jimcan92/research-weather-station/docs/schematic-mosfet-switch.html

# MOSFET Switch — 12V Wind Sensor Power

IRF4905 (P-channel) + 2N7000 (N-channel) · high-side switch · control from GPIO15

## Schematic

## How it works

GPIO15 | Q2 (2N7000) | Q1 (IRF4905) gate | 12V_SW output
LOW (0V) | OFF | pulled to +12V via R1 | 0V — sensors OFF
HIGH (3.3V) | ON | pulled to GND | 12V — sensors ON

Ngano ingon ani: Ang ESP32 3.3V ra ang iyang i-output, pero ang wind sensors nagkinahanglan og 12V. Ang 2N7000 (gagmay, 3.3V-driven) maoy mo-pull-down sa gate sa IRF4905 (dako, 12V) aron mo-ON kini. Ang R1 (10k) kay pull-up — nag-keep sa IRF4905 nga OFF by default para dili aksidente nga mo-on ang 12V samtang natulog ang ESP32.

## Parts list

Ref | Part | Type | Role
Q1 | IRF4905 | P-channel MOSFET (TO-220) | 12V high-side switch
Q2 | 2N7000 | N-channel MOSFET (TO-92) | Level shifter (3.3V → drive Q1 gate)
R1 | 10kΩ | Resistor | Gate pull-up (default OFF)
R2 | 1kΩ | Resistor | Q2 gate resistor (limits GPIO current)
