jimcan92/research-weather-station/hardware/node-pcb/weather-node-complete-preview-1.png

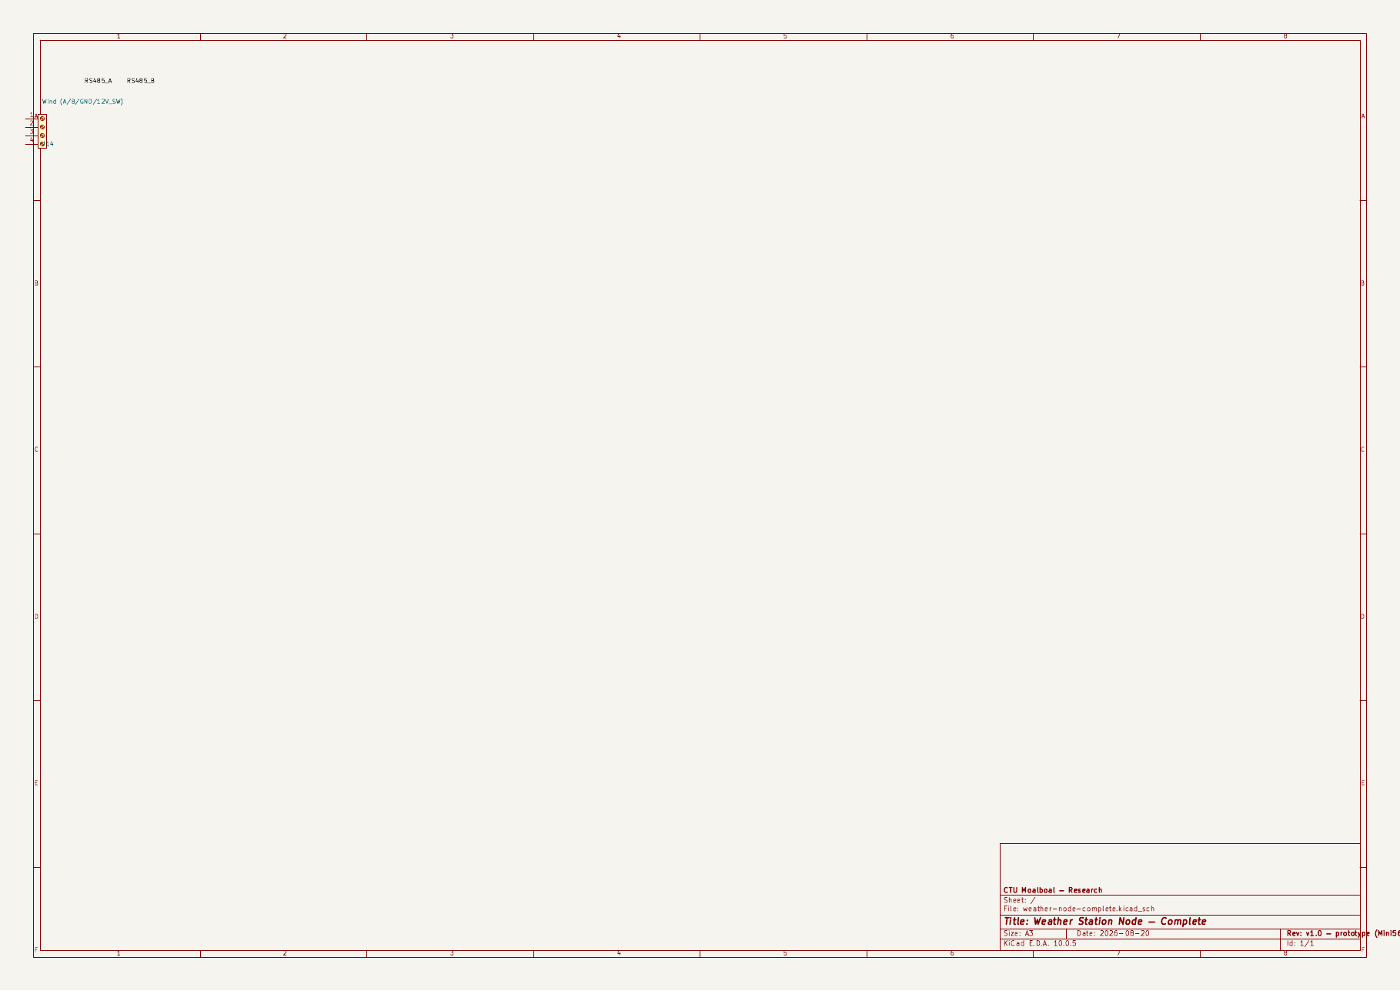
hardware/node-pcb/weather-node-complete-preview-1.png
