jimcan92/research-weather-station/output/schematic-review/lora-e22-current.png

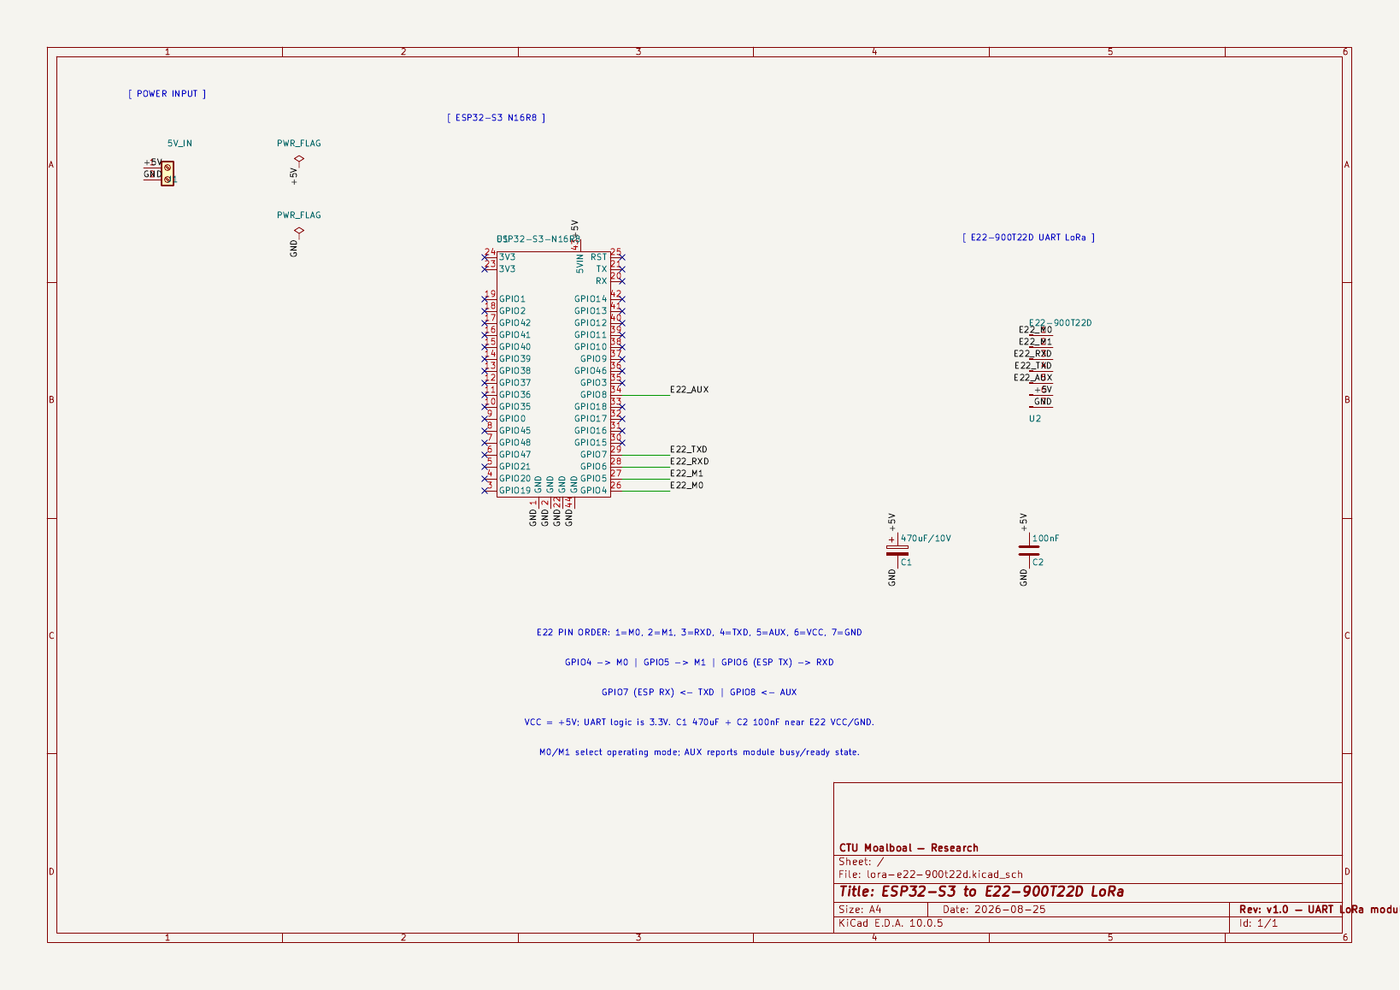
output/schematic-review/lora-e22-current.png
