jimcan92/research-weather-station/hardware/lora-e22/lora-e22-900t22d.kicad_sch

## KiCad design hardware/lora-e22/lora-e22-900t22d.kicad_sch (2026-09-29)

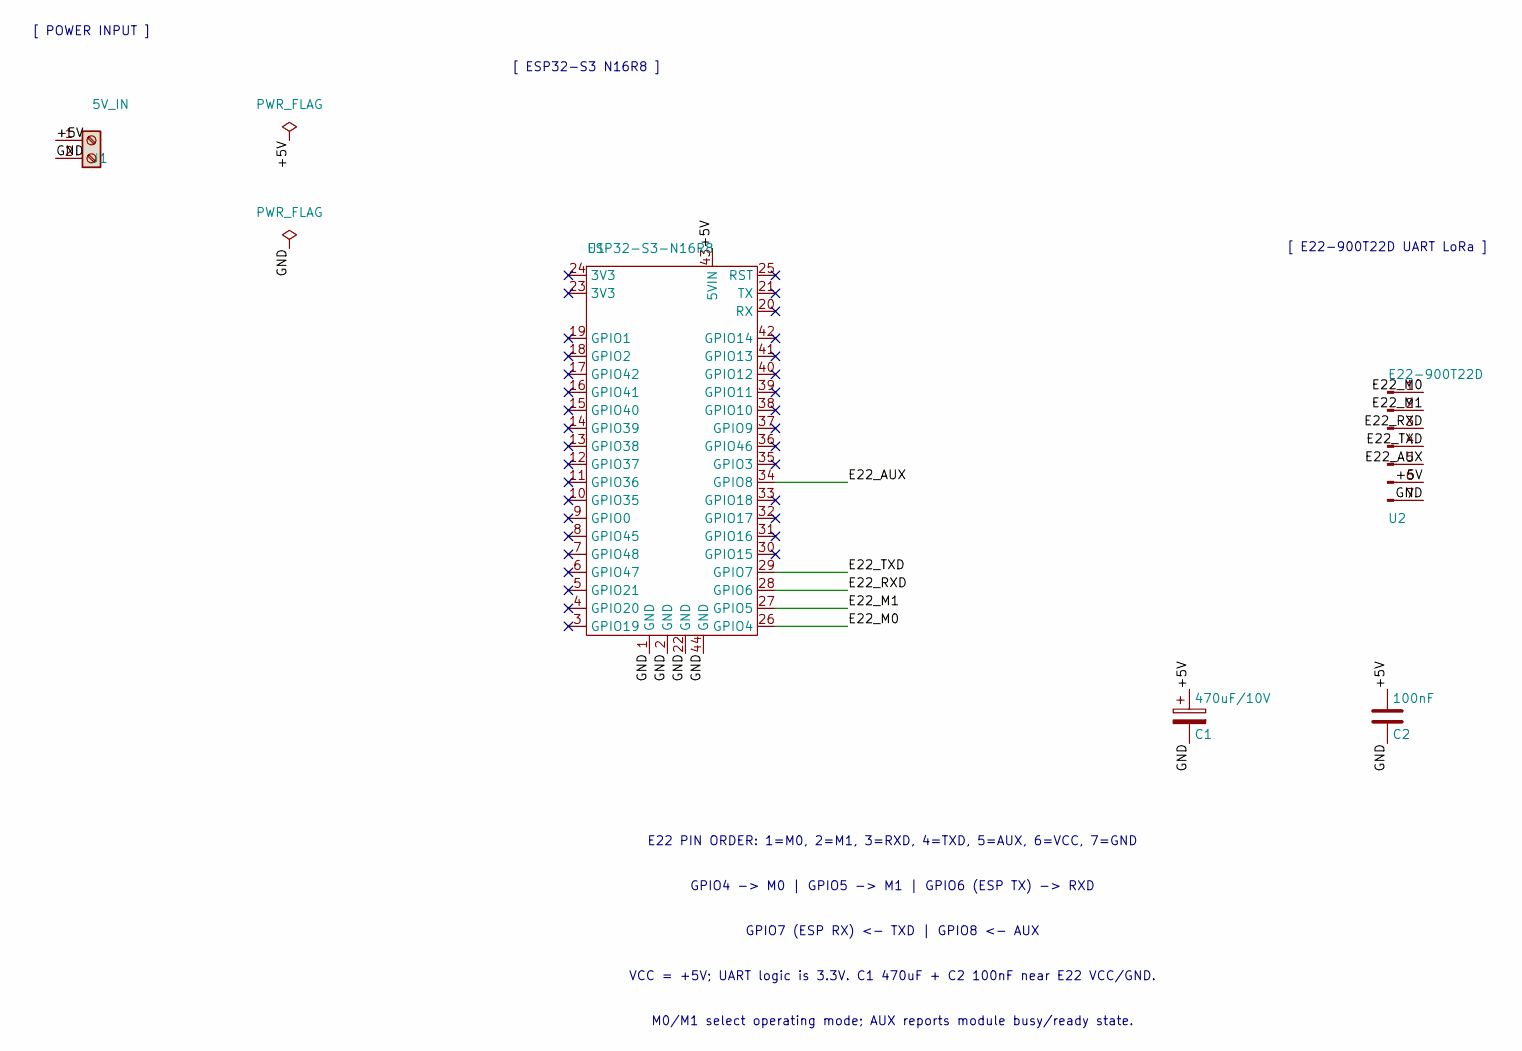
[picture p7: schematic lora-e22-900t22d.kicad_sch]

Parts:
C1: 470uF/10V
C2: 100nF
J1: 5V_IN
U1: ESP32-S3-N16R8
U2: E22-900T22D

Connections:
+5V: C1.1, C2.1, J1.1, U1.43 (5VIN), U2.6
E22_AUX: U1.34 (GPIO8), U2.5
E22_M0: U1.26 (GPIO4), U2.1
E22_M1: U1.27 (GPIO5), U2.2
E22_RXD: U1.28 (GPIO6), U2.3
E22_TXD: U1.29 (GPIO7), U2.4
GND: C1.2, C2.2, J1.2, U1.1 (GND), U1.2 (GND), U1.22 (GND), U1.44 (GND), U2.7

Notes on the sheet:
[ POWER INPUT ]
[ ESP32-S3 N16R8 ]
[ E22-900T22D UART LoRa ]
E22 PIN ORDER: 1=M0, 2=M1, 3=RXD, 4=TXD, 5=AUX, 6=VCC, 7=GND
GPIO4 -> M0 | GPIO5 -> M1 | GPIO6 (ESP TX) -> RXD
GPIO7 (ESP RX) <- TXD | GPIO8 <- AUX
VCC = +5V; UART logic is 3.3V. C1 470uF + C2 100nF near E22 VCC/GND.
M0/M1 select operating mode; AUX reports module busy/ready state.
