jimcan92/research-weather-station/hardware/node-pcb/weather-node-complete.kicad_sch

## KiCad design hardware/node-pcb/weather-node-complete.kicad_sch (2026-09-29)

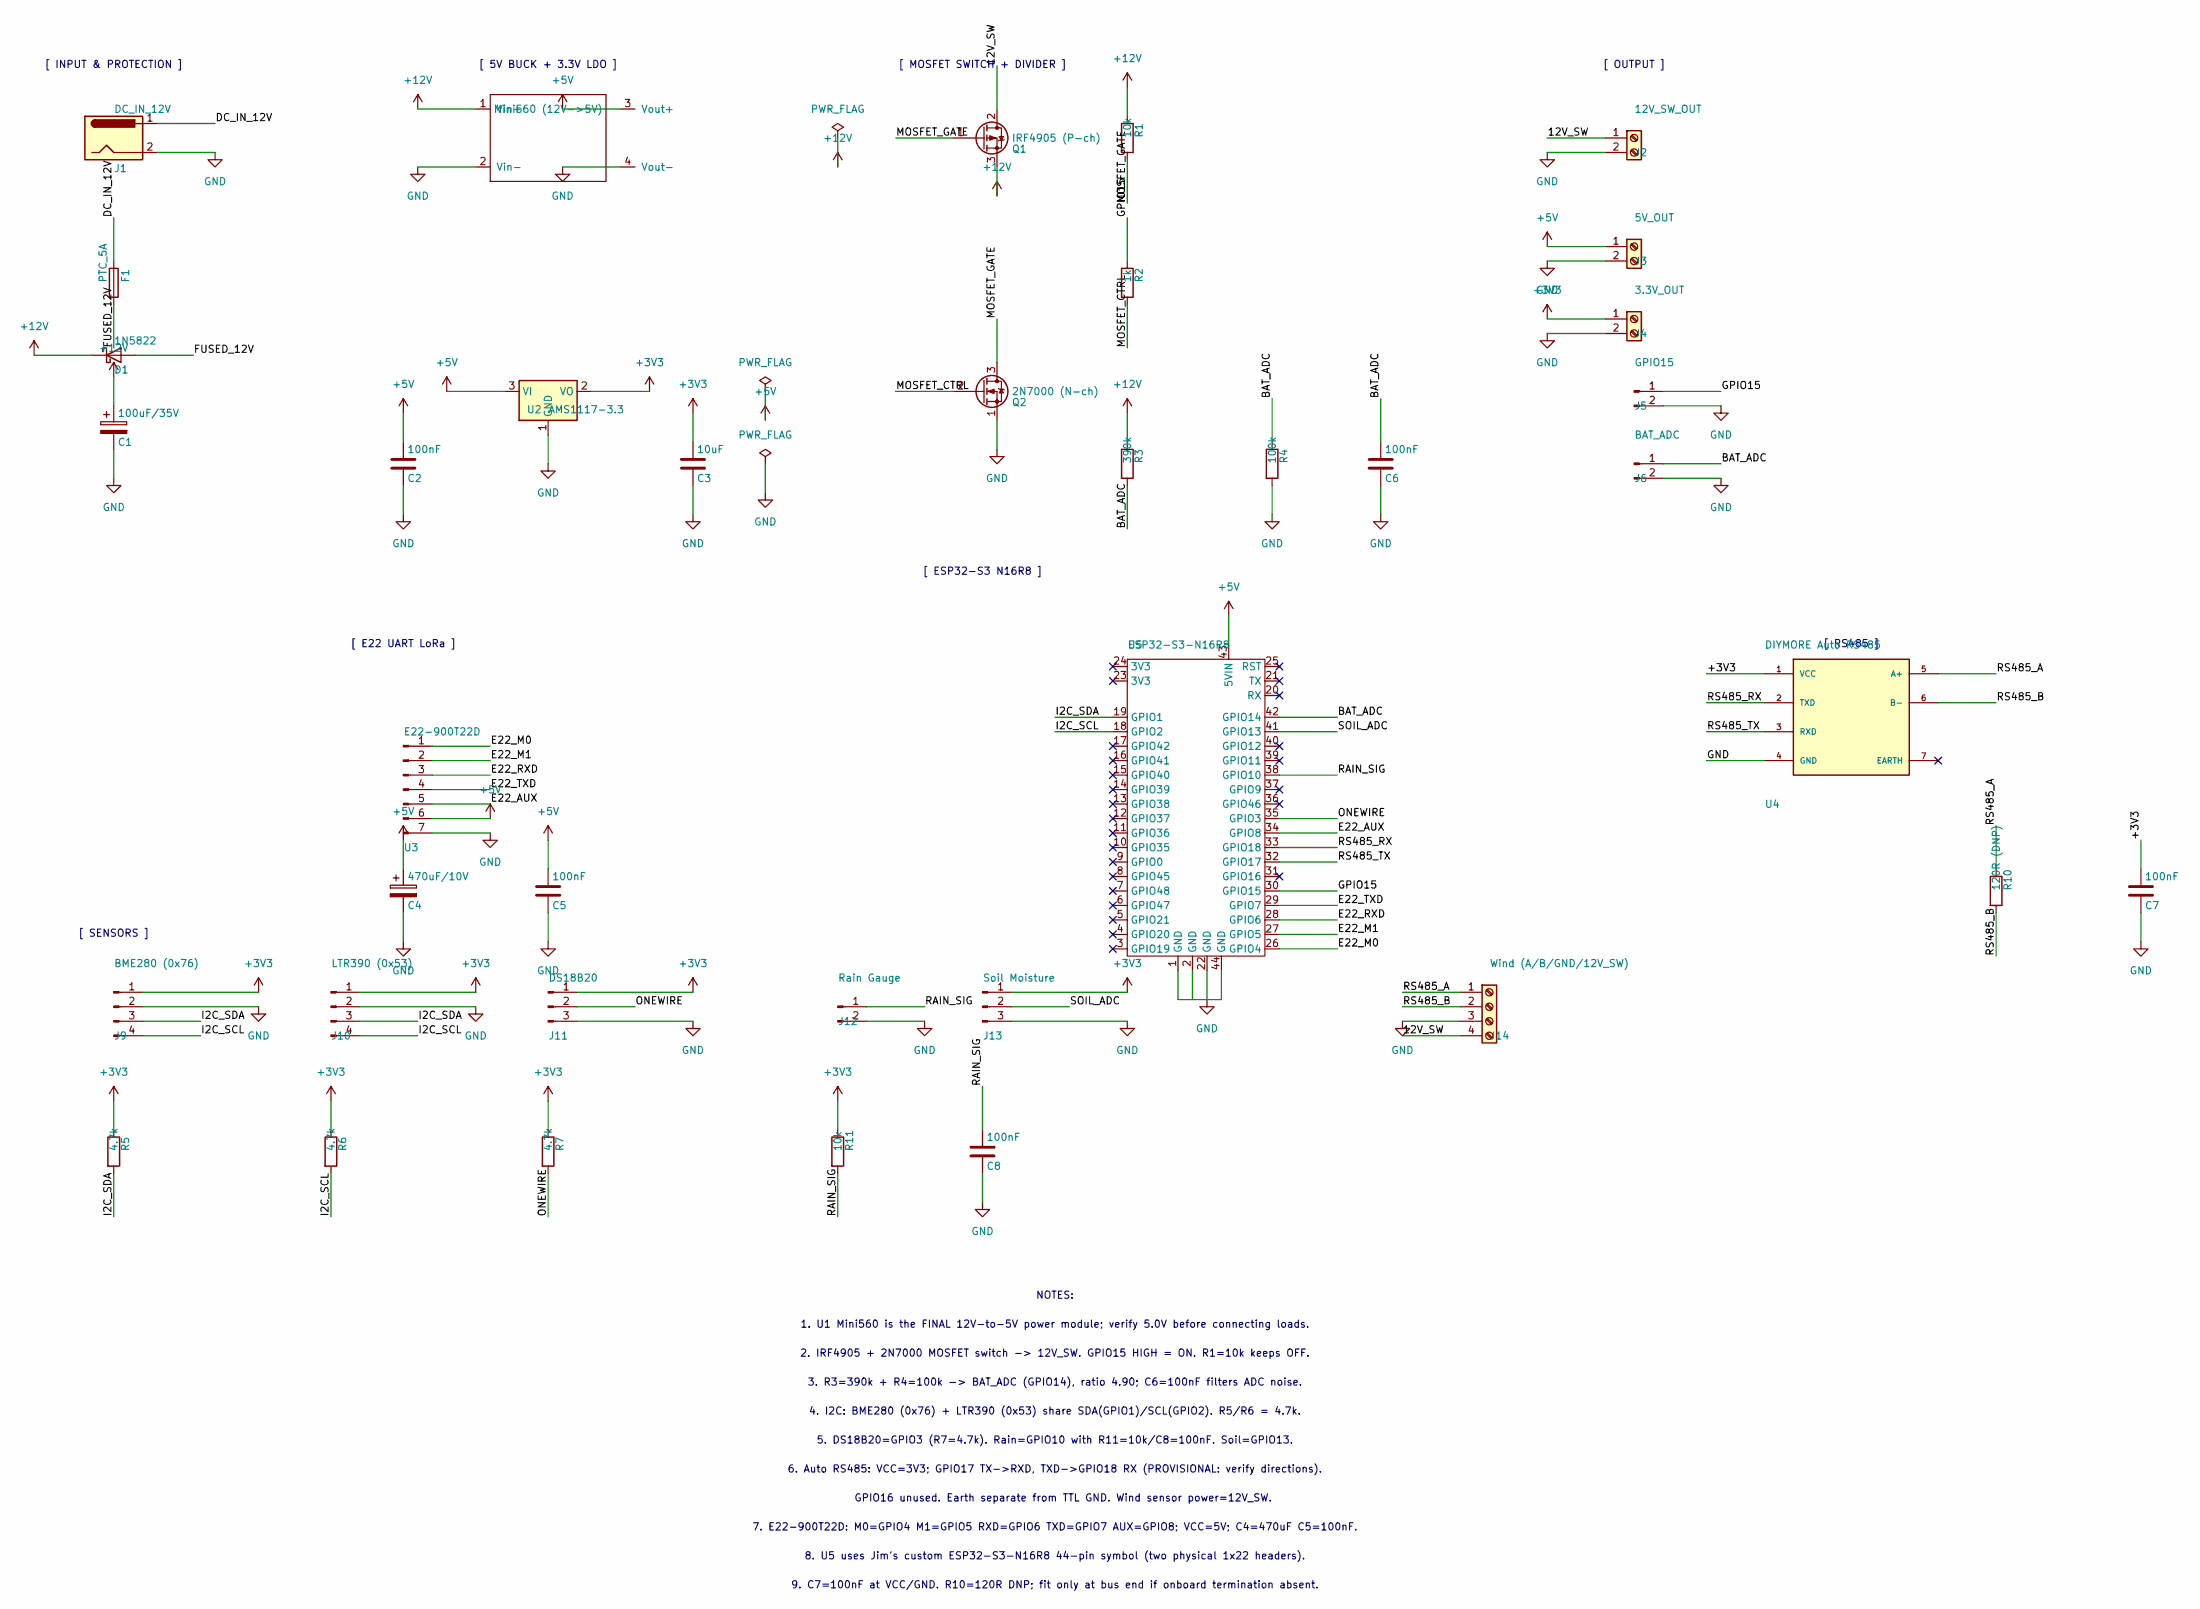
[picture p8: schematic weather-node-complete.kicad_sch]

Parts:
C1: 100uF/35V
C2, C5, C6, C7, C8: 100nF
C3: 10uF
C4: 470uF/10V
D1: 1N5822
F1: PTC_5A
J1: DC_IN_12V
J2: 12V_SW_OUT
J3: 5V_OUT
J4: 3.3V_OUT
J5: GPIO15
J6: BAT_ADC
J9: BME280 (0x76)
J10: LTR390 (0x53)
J11: DS18B20
J12: Rain Gauge
J13: Soil Moisture
J14: Wind (A/B/GND/12V_SW)
Q1: IRF4905 (P-ch)
Q2: 2N7000 (N-ch)
R1, R11: 10k
R2: 1k
R3: 390k
R4: 100k
R5, R6, R7: 4.7k
R10: 120R (DNP)
U1: Mini560 (12V->5V)
U2: AMS1117-3.3
U3: E22-900T22D
U4: DIYMORE Auto RS485
U5: ESP32-S3-N16R8

Connections:
12V_SW: J2.1, J14.4, Q1.2 (D)
+3V3: C3.1, C7.1, J4.1, J9.1, J10.1, J11.1, J13.1, R5.1, R6.1, R7.1, R11.1, U2.2 (VO), U4.1 (VCC)
+5V: C2.1, C4.1, C5.1, J3.1, U1.3 (Vout+), U2.3 (VI), U3.6, U5.43 (5VIN)
+12V: C1.1, D1.1 (K), Q1.3 (S), R1.1, R3.1, U1.1 (Vin+)
BAT_ADC: C6.1, J6.1, R3.2, R4.1, U5.42 (GPIO14)
DC_IN_12V: F1.1, J1.1
E22_AUX: U3.5, U5.34 (GPIO8)
E22_M0: U3.1, U5.26 (GPIO4)
E22_M1: U3.2, U5.27 (GPIO5)
E22_RXD: U3.3, U5.28 (GPIO6)
E22_TXD: U3.4, U5.29 (GPIO7)
FUSED_12V: D1.2 (A), F1.2
GND: C1.2, C2.2, C3.2, C4.2, C5.2, C6.2, C7.2, C8.2, J1.2, J2.2, J3.2, J4.2, J5.2, J6.2, J9.2, J10.2, J11.3, J12.2, J13.3, J14.3, Q2.1 (S), R4.2, U1.2 (Vin-), U1.4 (Vout-), U2.1 (GND), U3.7, U4.4 (GND), U5.1 (GND), U5.2 (GND), U5.22 (GND), U5.44 (GND)
GPIO15: J5.1, R2.1, U5.30 (GPIO15)
I2C_SCL: J9.4, J10.4, R6.2, U5.18 (GPIO2)
I2C_SDA: J9.3, J10.3, R5.2, U5.19 (GPIO1)
MOSFET_CTRL: Q2.2 (G), R2.2
MOSFET_GATE: Q1.1 (G), Q2.3 (D), R1.2
ONEWIRE: J11.2, R7.2, U5.35 (GPIO3)
RAIN_SIG: C8.1, J12.1, R11.2, U5.38 (GPIO10)
RS485_A: J14.1, R10.1, U4.5 (A+)
RS485_B: J14.2, R10.2, U4.6 (B-)
RS485_RX: U4.2 (TXD), U5.33 (GPIO18)
RS485_TX: U4.3 (RXD), U5.32 (GPIO17)
SOIL_ADC: J13.2, U5.41 (GPIO13)

Notes on the sheet:
[ INPUT & PROTECTION ]
[ 5V BUCK + 3.3V LDO ]
[ MOSFET SWITCH + DIVIDER ]
[ OUTPUT ]
[ ESP32-S3 N16R8 ]
[ E22 UART LoRa ]
[ RS485 ]
[ SENSORS ]
NOTES:
1. U1 Mini560 is the FINAL 12V-to-5V power module; verify 5.0V before connecting loads.
2. IRF4905 + 2N7000 MOSFET switch -> 12V_SW. GPIO15 HIGH = ON. R1=10k keeps OFF.
3. R3=390k + R4=100k -> BAT_ADC (GPIO14), ratio 4.90; C6=100nF filters ADC noise.
4. I2C: BME280 (0x76) + LTR390 (0x53) share SDA(GPIO1)/SCL(GPIO2). R5/R6 = 4.7k.
5. DS18B20=GPIO3 (R7=4.7k). Rain=GPIO10 with R11=10k/C8=100nF. Soil=GPIO13.
6. Auto RS485: VCC=3V3; GPIO17 TX->RXD, TXD->GPIO18 RX (PROVISIONAL: verify directions).
GPIO16 unused. Earth separate from TTL GND. Wind sensor power=12V_SW.
7. E22-900T22D: M0=GPIO4 M1=GPIO5 RXD=GPIO6 TXD=GPIO7 AUX=GPIO8; VCC=5V; C4=470uF C5=100nF.
8. U5 uses Jim's custom ESP32-S3-N16R8 44-pin symbol (two physical 1x22 headers).
9. C7=100nF at VCC/GND. R10=120R DNP; fit only at bus end if onboard termination absent.
