jimcan92/research-weather-station/hardware/node-pcb/weather-node.kicad_sch

## KiCad design hardware/node-pcb/weather-node.kicad_sch (2026-09-29)

Schematic: weather-node.kicad_sch

Parts:
J1: 12V_IN
J2: 5V_IN
J3: 3.3V_IN
J4: ESP32-S3 J1 (Left); PinHeader_2x11_P2.54mm_Vertical
J5: ESP32-S3 J3 (Right); PinHeader_2x11_P2.54mm_Vertical
J6: DS18B20; PinHeader_1x03_P2.54mm_Vertical
J7: Rain Gauge; PinHeader_1x02_P2.54mm_Vertical
J8: Soil Moisture; PinHeader_1x03_P2.54mm_Vertical
J9: Wind Sensor (RS485)
Q1: IRF9540N
Q2: 2N7000
R1: 10k
R2: 1k
R3: 330k
R4: 100k
R5, R6, R7: 4.7k
U1: SX1278 LoRa
U2: BME280 (0x76)
U3: LTR390 (0x53)
U4: MAX485; DIP-8_W7.62mm

Notes on the sheet:
=== POWER SECTION ===
=== MCU — ESP32-S3 HW678 N16R8 ===
=== LoRa — SX1278 915 MHz ===
=== I2C Sensors ===
=== OneWire ===
=== Digital / Analog ===
=== RS485 — Wind Sensors ===
NOTES:
1. I2C bus: BME280 (0x76) + LTR390 (0x53) share SDA/SCL pins — no address conflict
2. RS485: Anemometer (ID1) + Wind Vane (ID2) share same A/B bus
3. Pull-ups required: SDA/SCL (4.7k to 3.3V), DS18B20 DQ (4.7k to 3.3V)
4. ESP32-S3 HW678 N16R8 — 16MB Flash, 8MB Octal PSRAM. GPIO35-37 reserved.
5. Q1+Q2 form 12V level-shifted switch (GPIO15 3.3V drives IRF9540N gate via 2N7000).
6. Battery ADC divider: 330k + 100k (ratio 4.30). 12.6V full → 2.93V at ADC pin.
