jimcan92/research-weather-station/hardware/power-pcb/weather-power-v3.kicad_sch

## KiCad design hardware/power-pcb/weather-power-v3.kicad_sch (2026-09-29)

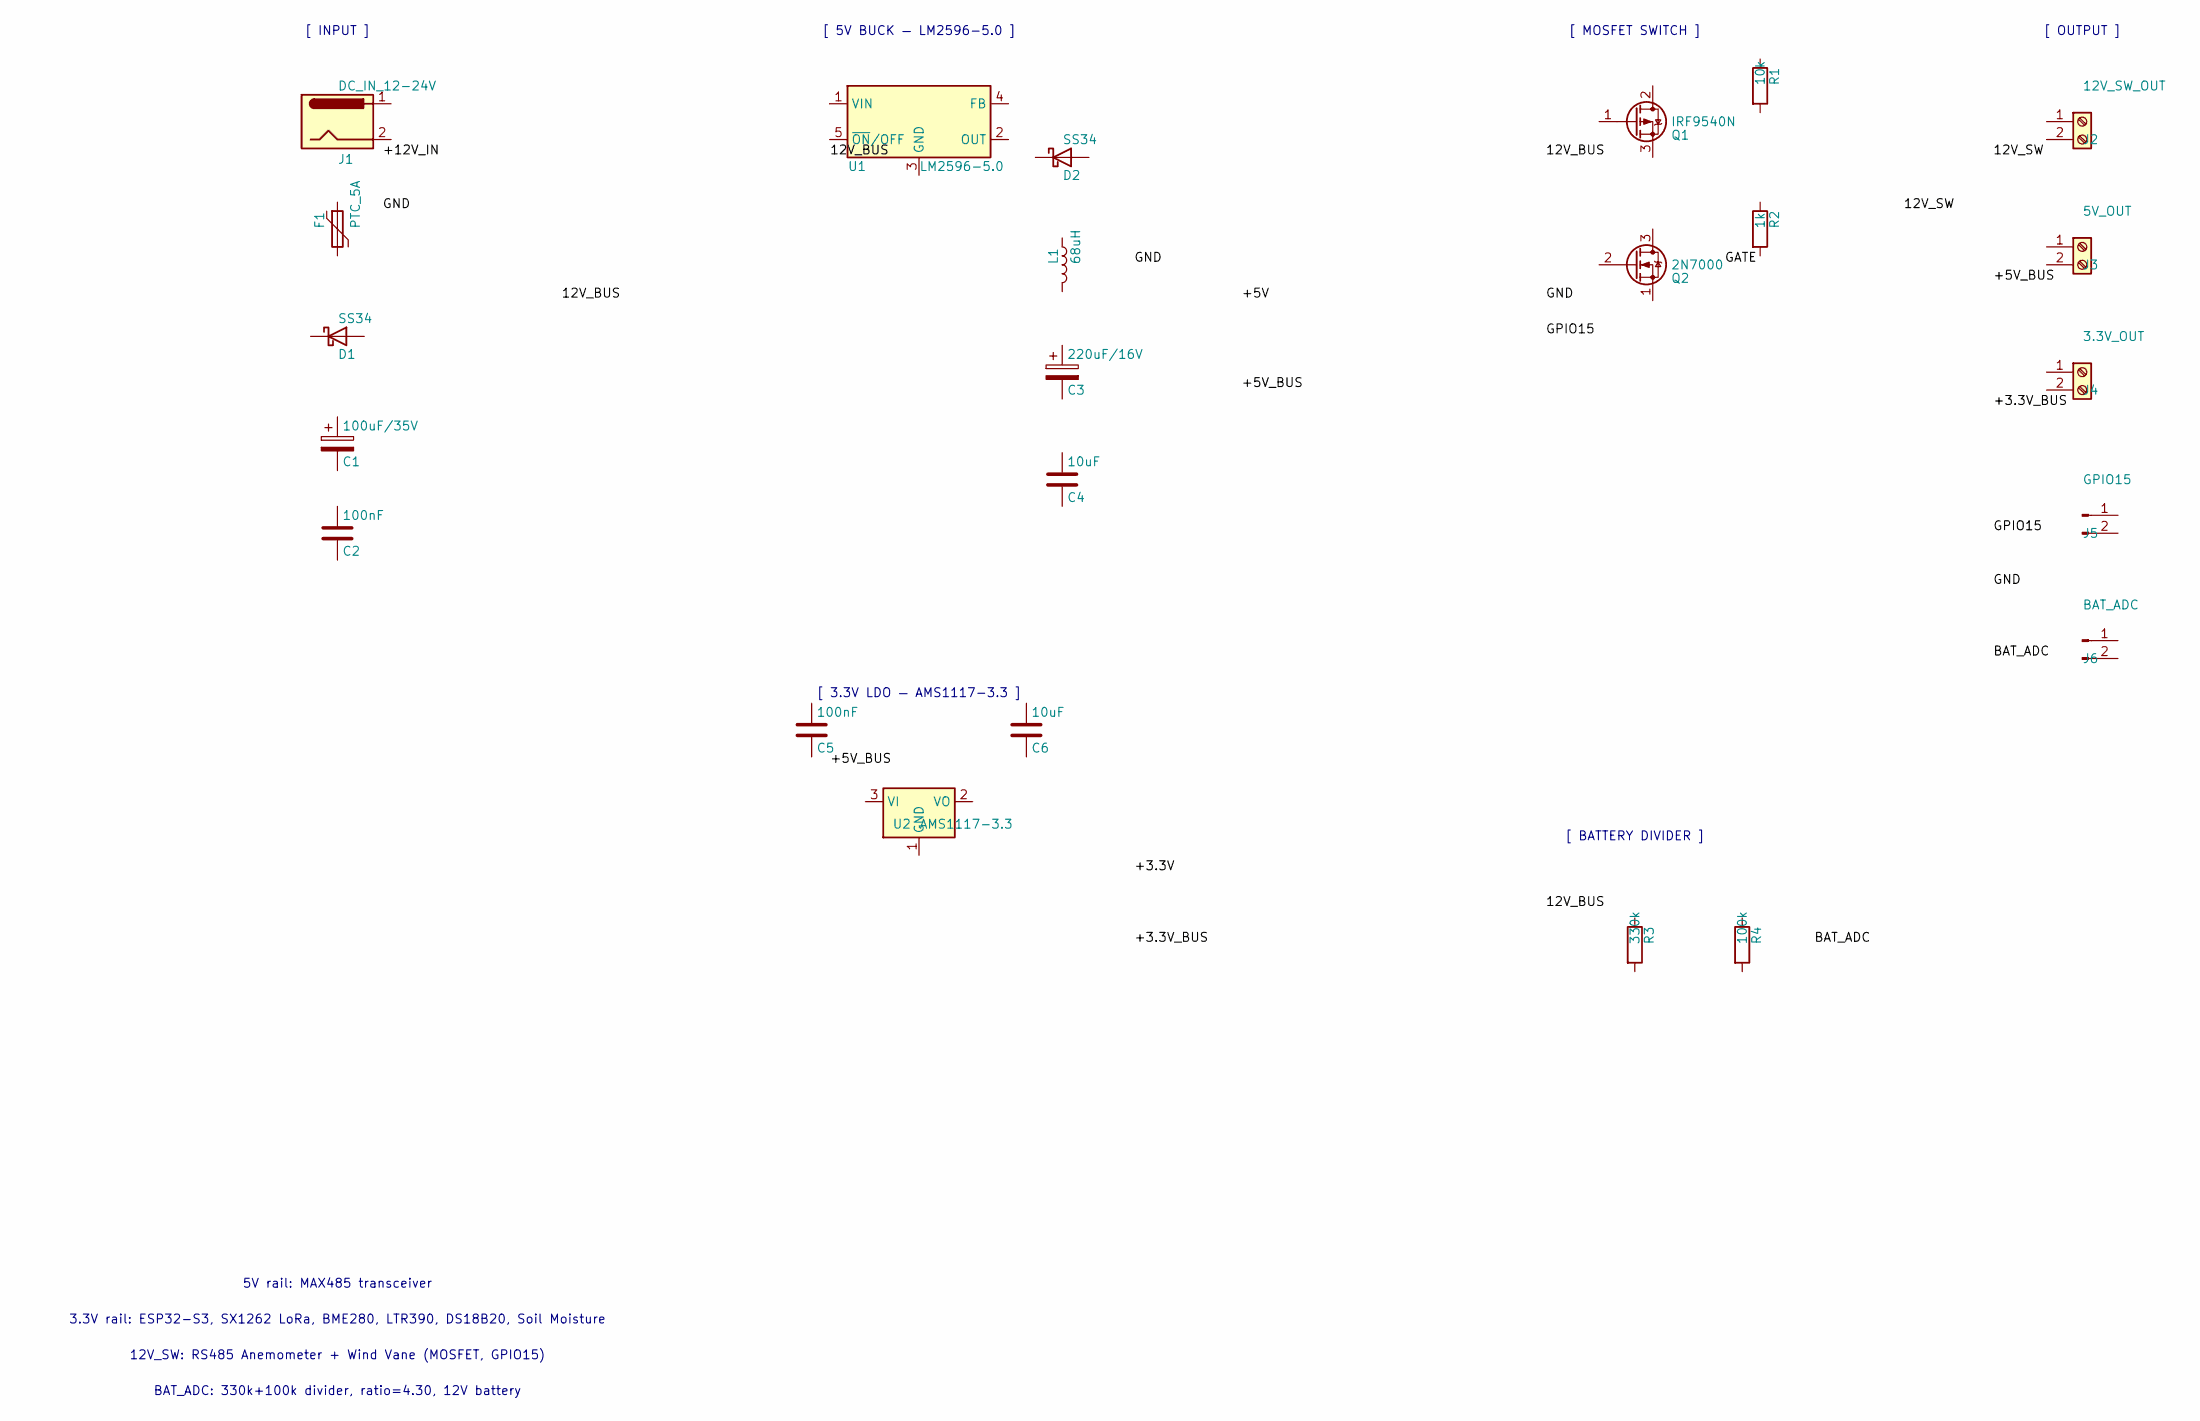
[picture p9: schematic weather-power-v3.kicad_sch]

Parts:
C1: 100uF/35V
C2, C5: 100nF
C3: 220uF/16V
C4, C6: 10uF
D1, D2: SS34
F1: PTC_5A
J1: DC_IN_12-24V
J2: 12V_SW_OUT
J3: 5V_OUT
J4: 3.3V_OUT
J5: GPIO15
J6: BAT_ADC
L1: 68uH
Q1: IRF9540N
Q2: 2N7000
R1: 10k
R2: 1k
R3: 330k
R4: 100k
U1: LM2596-5.0
U2: AMS1117-3.3

Notes on the sheet:
[ INPUT ]
[ 5V BUCK — LM2596-5.0 ]
[ 3.3V LDO — AMS1117-3.3 ]
[ MOSFET SWITCH ]
[ BATTERY DIVIDER ]
[ OUTPUT ]
5V rail: MAX485 transceiver
3.3V rail: ESP32-S3, SX1262 LoRa, BME280, LTR390, DS18B20, Soil Moisture
12V_SW: RS485 Anemometer + Wind Vane (MOSFET, GPIO15)
BAT_ADC: 330k+100k divider, ratio=4.30, 12V battery
