jimcan92/research-weather-station/hardware/power-supply/power-supply.kicad_sch

## KiCad design hardware/power-supply/power-supply.kicad_sch (2026-09-29)

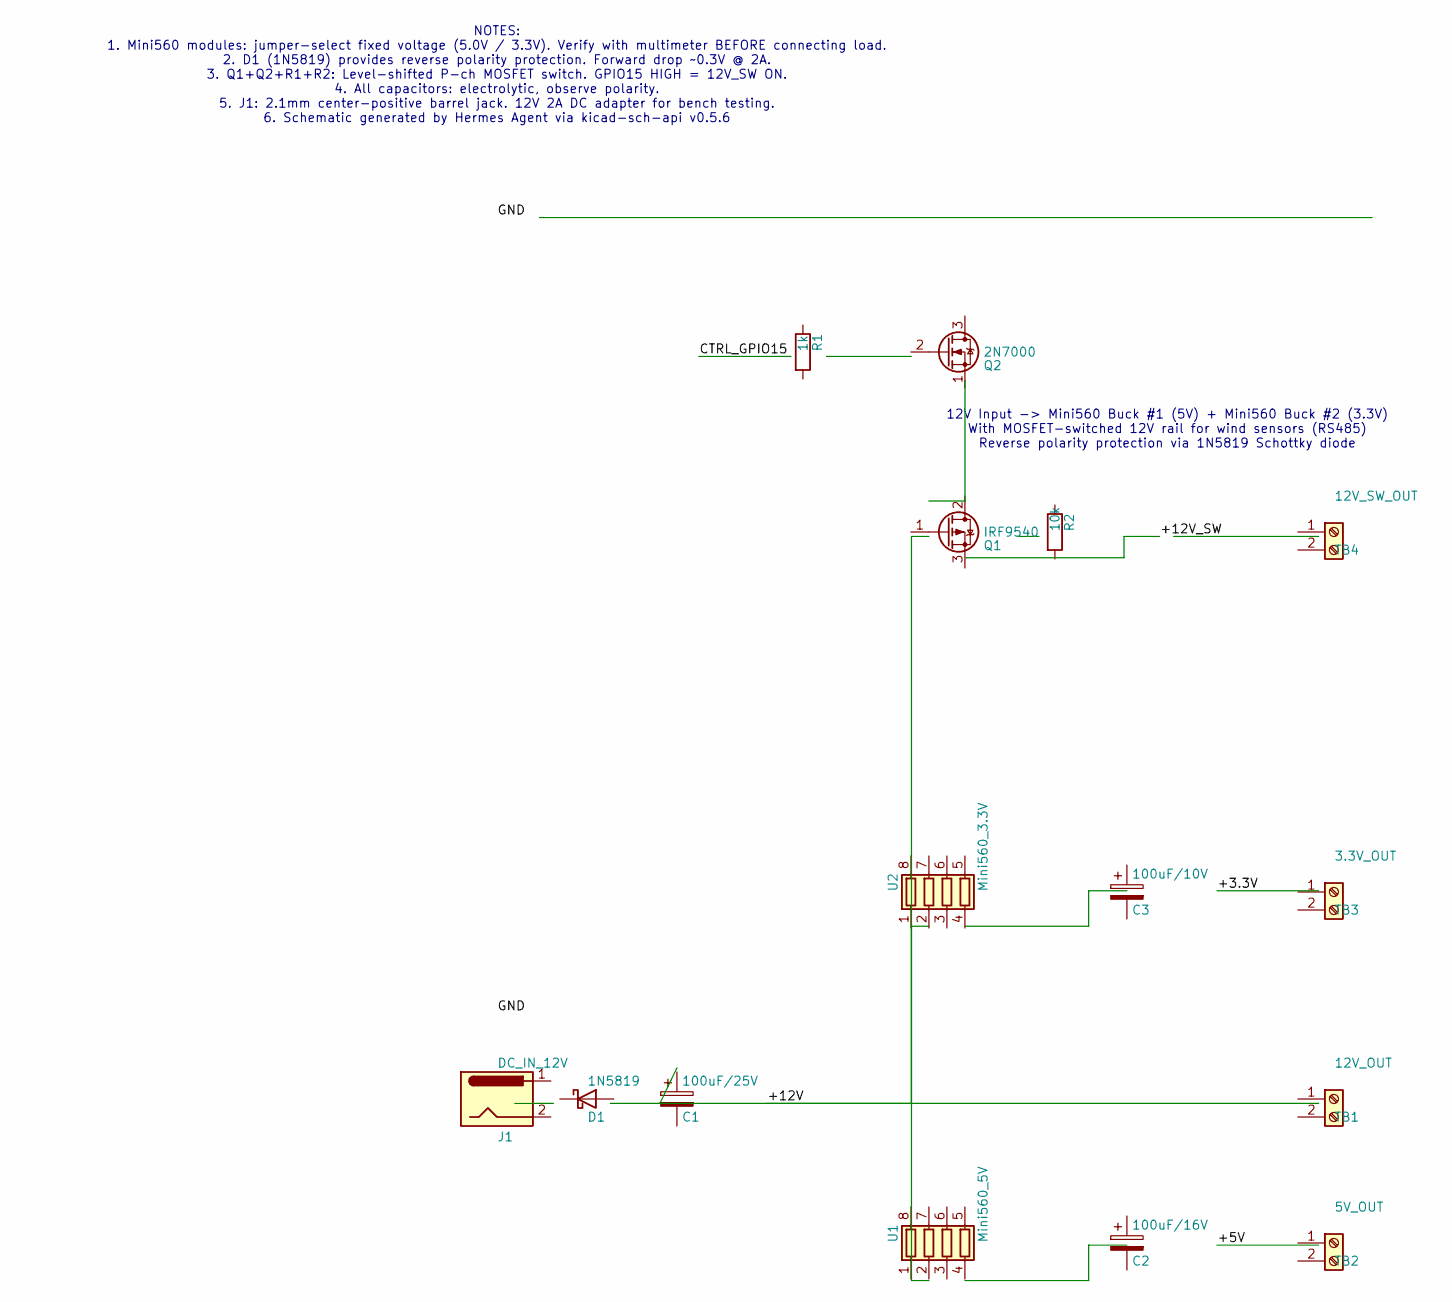
[picture p10: schematic power-supply.kicad_sch]

Parts:
C1: 100uF/25V; CP_Radial_D8.0mm_P3.50mm
C2: 100uF/16V; CP_Radial_D6.3mm_P2.50mm
C3: 100uF/10V; CP_Radial_D6.3mm_P2.50mm
D1: 1N5819; D_DO-41_SOD81_P7.62mm_Horizontal
J1: DC_IN_12V; BarrelJack_CUI_PJ-063AH_Horizontal
Q1: IRF9540; TO-220-3_Vertical
Q2: 2N7000; TO-92-3_Inline
R1: 1k; R_Axial_DIN0207_L6.3mm_D2.5mm_P10.16mm_Horizontal
R2: 10k; R_Axial_DIN0207_L6.3mm_D2.5mm_P10.16mm_Horizontal
TB1: 12V_OUT; TerminalBlock_bornier-2_P5.08mm
TB2: 5V_OUT; TerminalBlock_bornier-2_P5.08mm
TB3: 3.3V_OUT; TerminalBlock_bornier-2_P5.08mm
TB4: 12V_SW_OUT; TerminalBlock_bornier-2_P5.08mm
U1: Mini560_5V; Mini560
U2: Mini560_3.3V; Mini560

Notes on the sheet:
12V Input -> Mini560 Buck #1 (5V) + Mini560 Buck #2 (3.3V) With MOSFET-switched 12V rail for wind sensors (RS485) Reverse polarity protection via 1N5819 Schottky diode
NOTES: 1. Mini560 modules: jumper-select fixed voltage (5.0V / 3.3V). Verify with multimeter BEFORE connecting load. 2. D1 (1N5819) provides reverse polarity protection. Forward drop ~0.3V @ 2A. 3. Q1+Q2+R1+R2: Level-shifted P-ch MOSFET switch. GPIO15 HIGH = 12V_SW ON. 4. All capacitors: electrolyt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
