jimcan92/research-weather-station/output/schematic-review/weather-node-complete-before-final.kicad_sch

## KiCad design output/schematic-review/weather-node-complete-before-final.kicad_sch (2026-09-29)

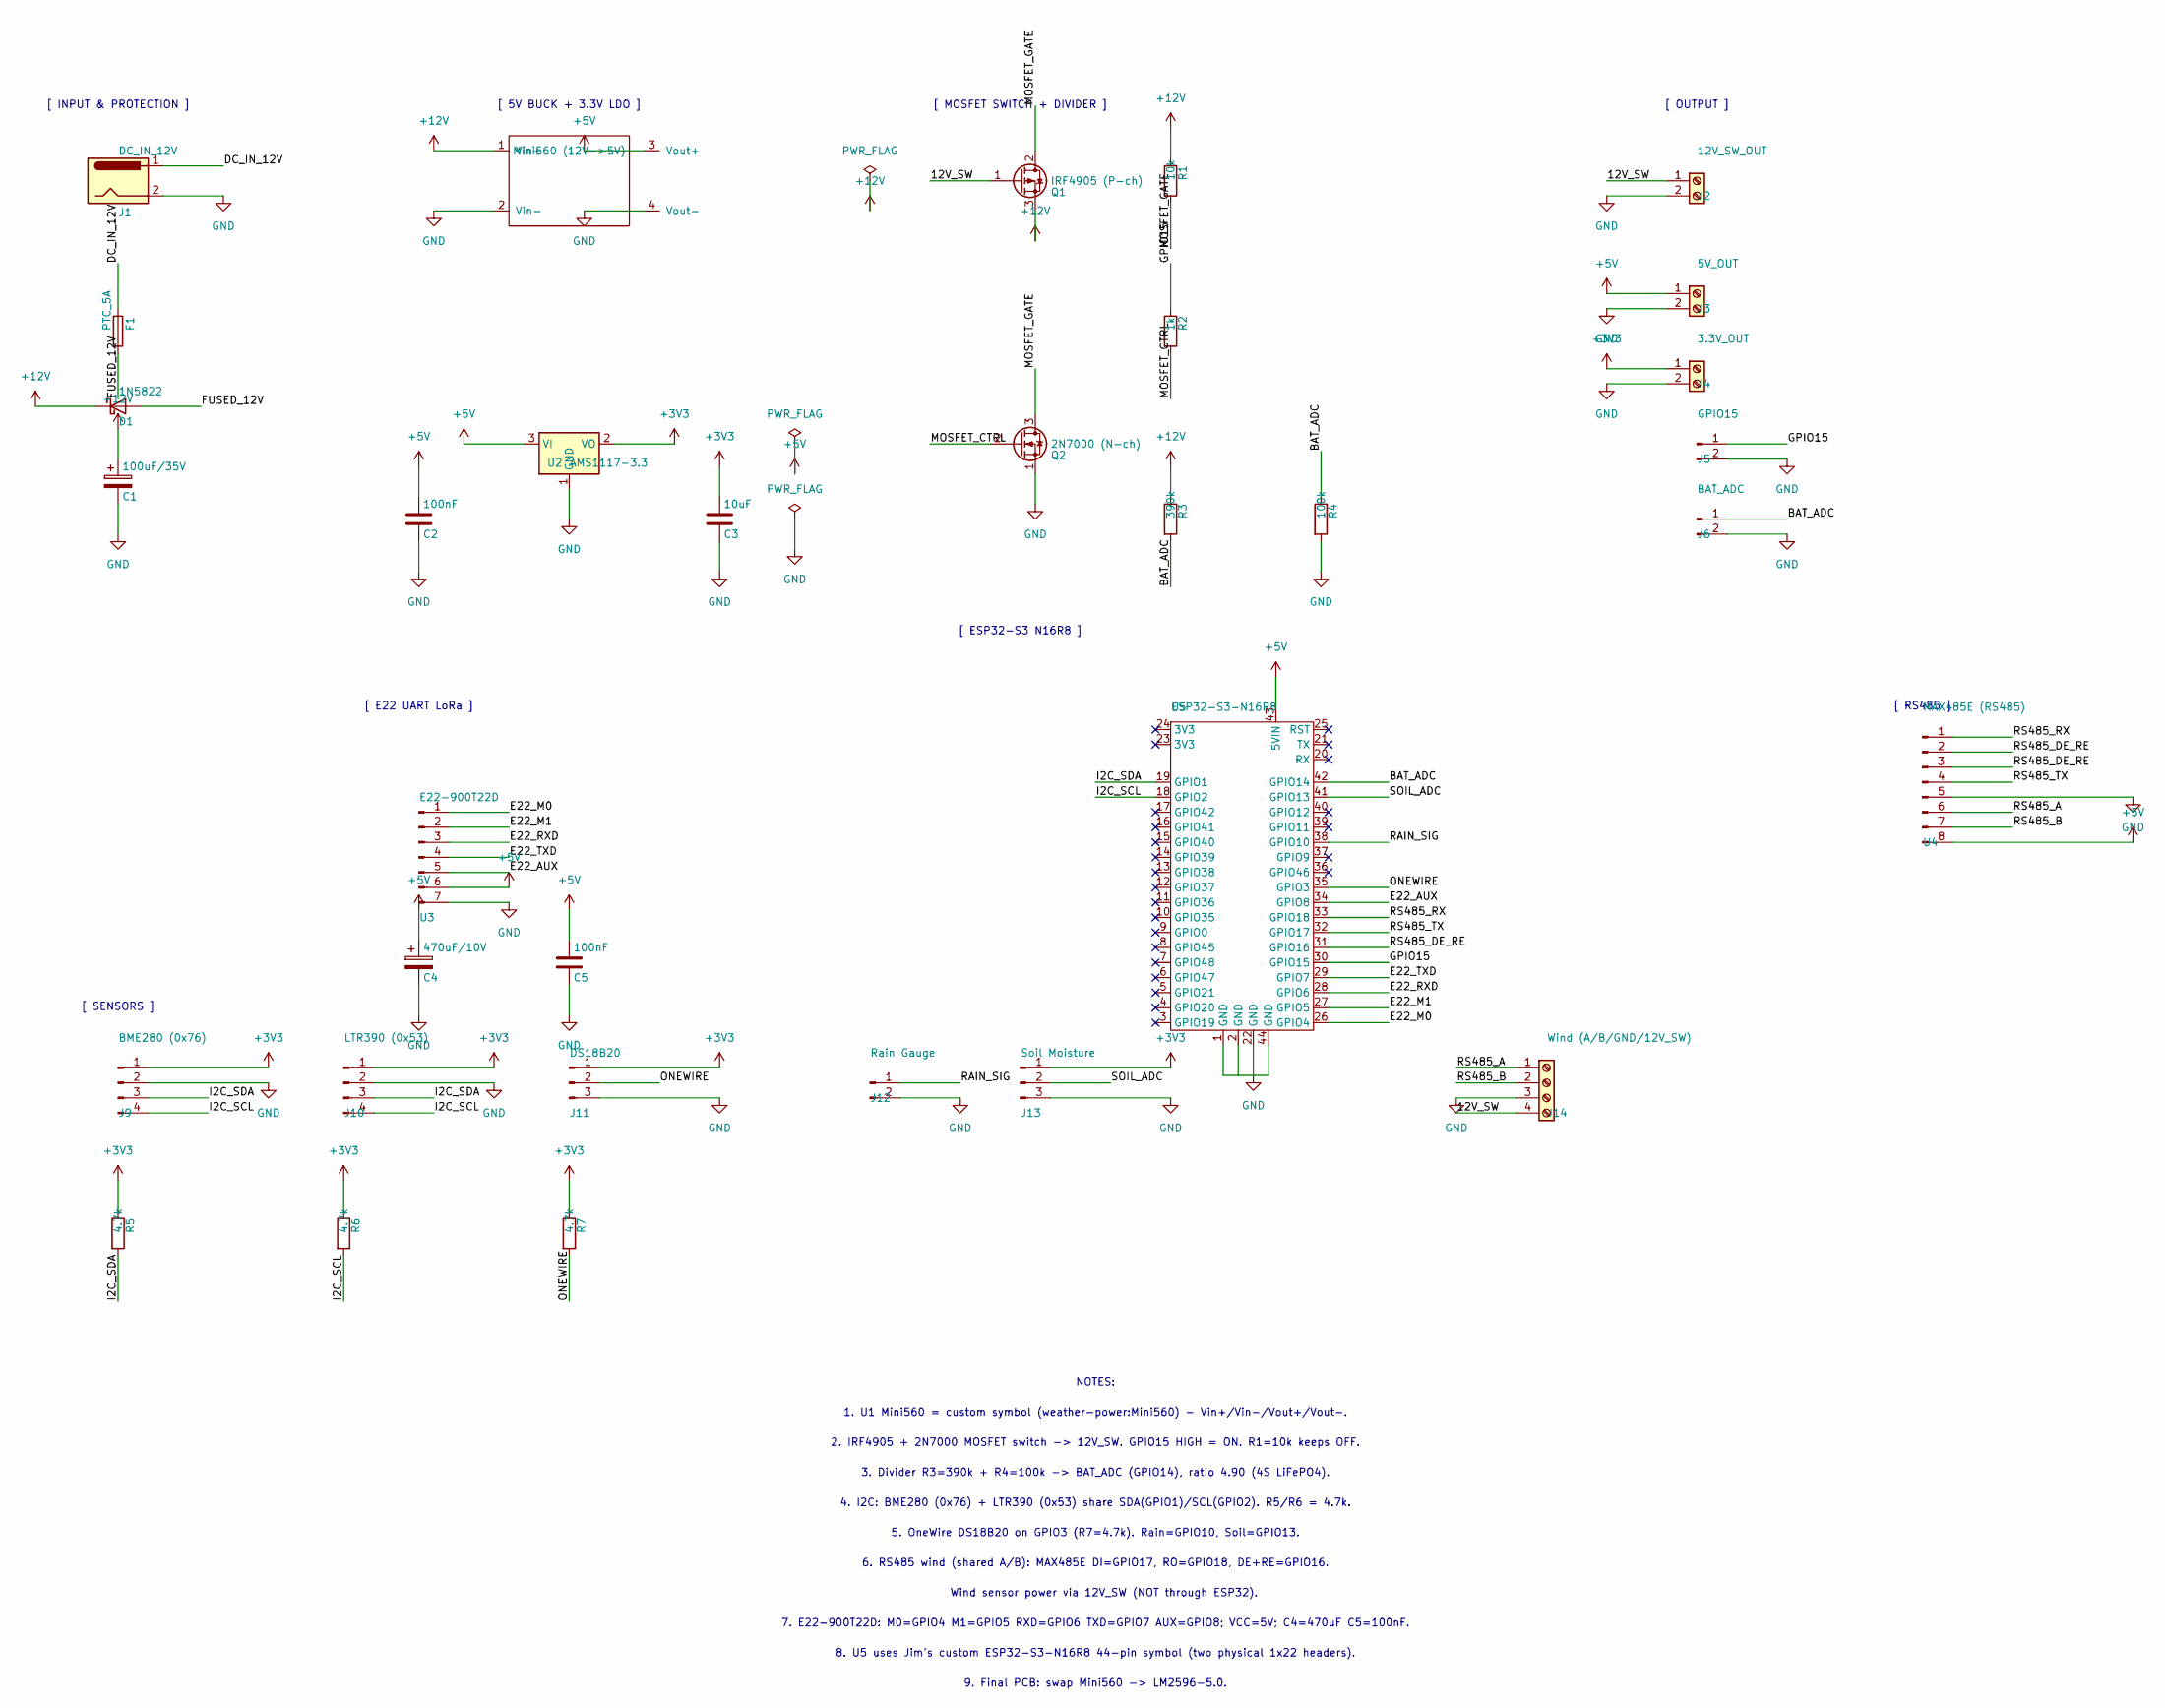
[picture p11: schematic weather-node-complete-before-final.kicad_sch]

Parts:
C1: 100uF/35V
C2, C5: 100nF
C3: 10uF
C4: 470uF/10V
D1: 1N5822
F1: PTC_5A
J1: DC_IN_12V
J2: 12V_SW_OUT
J3: 5V_OUT
J4: 3.3V_OUT
J5: GPIO15
J6: BAT_ADC
J9: BME280 (0x76)
J10: LTR390 (0x53)
J11: DS18B20
J12: Rain Gauge
J13: Soil Moisture
J14: Wind (A/B/GND/12V_SW)
Q1: IRF4905 (P-ch)
Q2: 2N7000 (N-ch)
R1: 10k
R2: 1k
R3: 390k
R4: 100k
R5, R6, R7: 4.7k
U1: Mini560 (12V->5V)
U2: AMS1117-3.3
U3: E22-900T22D
U4: MAX485E (RS485)
U5: ESP32-S3-N16R8

Connections:
12V_SW: J2.1, J14.4, Q1.1 (G)
+3V3: C3.1, J4.1, J9.1, J10.1, J11.1, J13.1, R5.1, R6.1, R7.1, U2.2 (VO)
+5V: C2.1, C4.1, C5.1, J3.1, U1.3 (Vout+), U2.3 (VI), U3.6, U4.8, U5.43 (5VIN)
+12V: C1.1, D1.1 (K), Q1.3 (S), R1.1, R3.1, U1.1 (Vin+)
BAT_ADC: J6.1, R3.2, R4.1, U5.42 (GPIO14)
DC_IN_12V: F1.1, J1.1
E22_AUX: U3.5, U5.34 (GPIO8)
E22_M0: U3.1, U5.26 (GPIO4)
E22_M1: U3.2, U5.27 (GPIO5)
E22_RXD: U3.3, U5.28 (GPIO6)
E22_TXD: U3.4, U5.29 (GPIO7)
FUSED_12V: D1.2 (A), F1.2
GND: C1.2, C2.2, C3.2, C4.2, C5.2, J1.2, J2.2, J3.2, J4.2, J5.2, J6.2, J9.2, J10.2, J11.3, J12.2, J13.3, J14.3, Q2.1 (S), R4.2, U1.2 (Vin-), U1.4 (Vout-), U2.1 (GND), U3.7, U4.5, U5.1 (GND), U5.2 (GND), U5.22 (GND), U5.44 (GND)
GPIO15: J5.1, R2.1, U5.30 (GPIO15)
I2C_SCL: J9.4, J10.4, R6.2, U5.18 (GPIO2)
I2C_SDA: J9.3, J10.3, R5.2, U5.19 (GPIO1)
MOSFET_CTRL: Q2.2 (G), R2.2
MOSFET_GATE: Q1.2 (D), Q2.3 (D), R1.2
ONEWIRE: J11.2, R7.2, U5.35 (GPIO3)
RAIN_SIG: J12.1, U5.38 (GPIO10)
RS485_A: J14.1, U4.6
RS485_B: J14.2, U4.7
RS485_DE_RE: U4.2, U4.3, U5.31 (GPIO16)
RS485_RX: U4.1, U5.33 (GPIO18)
RS485_TX: U4.4, U5.32 (GPIO17)
SOIL_ADC: J13.2, U5.41 (GPIO13)

Notes on the sheet:
[ INPUT & PROTECTION ]
[ 5V BUCK + 3.3V LDO ]
[ MOSFET SWITCH + DIVIDER ]
[ OUTPUT ]
[ ESP32-S3 N16R8 ]
[ E22 UART LoRa ]
[ RS485 ]
[ SENSORS ]
NOTES:
1. U1 Mini560 = custom symbol (weather-power:Mini560) - Vin+/Vin-/Vout+/Vout-.
2. IRF4905 + 2N7000 MOSFET switch -> 12V_SW. GPIO15 HIGH = ON. R1=10k keeps OFF.
3. Divider R3=390k + R4=100k -> BAT_ADC (GPIO14), ratio 4.90 (4S LiFePO4).
4. I2C: BME280 (0x76) + LTR390 (0x53) share SDA(GPIO1)/SCL(GPIO2). R5/R6 = 4.7k.
5. OneWire DS18B20 on GPIO3 (R7=4.7k). Rain=GPIO10, Soil=GPIO13.
6. RS485 wind (shared A/B): MAX485E DI=GPIO17, RO=GPIO18, DE+RE=GPIO16.
Wind sensor power via 12V_SW (NOT through ESP32).
7. E22-900T22D: M0=GPIO4 M1=GPIO5 RXD=GPIO6 TXD=GPIO7 AUX=GPIO8; VCC=5V; C4=470uF C5=100nF.
8. U5 uses Jim's custom ESP32-S3-N16R8 44-pin symbol (two physical 1x22 headers).
9. Final PCB: swap Mini560 -> LM2596-5.0.
