jimcan92/research-weather-station/firmware/weather-node/data/_app/immutable/nodes/2.DMCbWiEh.js

import{a as P,b as Cr,d as Mr,c as X,f as ae}from"../chunks/D1FSuJcD.js";import{o as Ir}from"../chunks/CMUUatgv.js";import{b as ha,h as k,a as Re,g as o,r as Pr,J as Or,c as ea,e as _e,i as le,j as ie,K as Rr,M as Fr,N as ta,O as ve,P as Pe,Q,R as Ae,T as Lr,U as jr,V as Hr,W as mt,X as $t,Y as Dr,Z as Vr,m as Wr,_ as aa,$ as zr,a0 as Br,a1 as ba,a2 as ga,a3 as ct,a4 as Gr,a5 as Ur,a6 as Yr,a7 as Fe,a8 as qr,a9 as ma,aa as $a,ab as ya,ac as Kr,ad as wa,ae as Xr,E as Zr,o as Jr,af as Sa,ag as Qr,ah as Na,l as Ea,ai as ra,aj as sa,ak as es,al as Aa,am as ts,an as as,ao as je,ap as rs,aq as ss,ar as ns,as as is,at as ls,au as os,av as fs,aw as ds,ax as cs,ay as us,w as vs,u as Le,n as ps,k as _s,t as xs,v as na,az as ia,aA as hs,aB as pe,aC as bs,aD as gs,q as Ta,z as ka,B as v,x as Z,y as x,C as u,G as Oe,aE as ms,F as Ie,I as j,aF as F,s as H,A as K}from"../chunks/BKZNgt86.js";import{i as $s,a as ys,d as se,b as Ca,c as ws,n as Ss,e as Ns,s as M}from"../chunks/Dv8ogEY2.js";import{l as Y,p as ce,s as ee,i as ue}from"../chunks/BygmMQg2.js";import{B as Es}from"../chunks/PEbfX-U0.js";function Ma(e,a){return a}function As(e,a,t){for(var r=[],s=a.length,l,n=a.length,i=0;i<s;i++){let g=a[i];ga(g,()=>{if(l){if(l.pending.delete(g),l.done.add(g),l.pending.size===0){var h=e.outrogroups;xt(e,$t(l.done)),h.delete(l),h.size===0&&(e.outrogroups=null)}}else n-=1},!1)}if(n===0){var c=r.length===0&&t!==null&&e.pending.size===0;if(c){var _=t,d=_.parentNode;Ur(d),d.append(_),e.items.clear()}xt(e,a,!c)}else l={pending:new Set(a),done:new Set},(e.outrogroups??(e.outrogroups=new Set)).add(l)}function xt(e,a,t=!0){var r;if(e.pending.size>0){r=new Set;for(const n of e.pending.values())for(const i of n)r.add(e.items.get(i).e)}for(var s=0;s<a.length;s++){var l=a[s];if(r!=null&&r.has(l)){l.f|=Q;const n=document.createDocumentFragment();Yr(l,n)}else Fe(a[s],t)}}var la;function Ia(e,a,t,r,s,l=null){var n=e,i=new Map,c=(a&$a)!==0;if(c){var _=e;n=k?_e(ma(_)):_.appendChild(Pe())}k&&Re();var d=null,g=Hr(()=>{var N=t();return mt(N)?N:N==null?[]:$t(N)}),h,y=new Map,b=!0;function A(N){(T.effect.f&Br)===0&&(T.pending.delete(N),T.fallback=d,Ts(T,h,n,a,r),d!==null&&(h.length===0?(d.f&Q)===0?ba(d):(d.f^=Q,Se(d,null,n)):ga(d,()=>{d=null})))}function p(N){T.pending.delete(N)}var w=ha(()=>{h=o(g);var N=h.length;let S=!1;if(k){var V=Pr(n)===Or;V!==(N===0)&&(n=ea(),_e(n),le(!1),S=!0)}for(var $=new Set,m=ve,C=jr(),O=0;O<N;O+=1){k&&ie.nodeType===Rr&&ie.data===Fr&&(n=ie,S=!0,le(!1));var I=h[O],z=r(I,O),R=b?null:i.get(z);R?(R.v&&ta(R.v,I),R.i&&ta(R.i,O),C&&m.unskip_effect(R.e)):(R=ks(i,b?n:la??(la=Pe()),I,z,O,s,a,t),b||(R.e.f|=Q),i.set(z,R)),$.add(z)}if(N===0&&l&&!d&&(b?d=Ae(()=>l(n)):(d=Ae(()=>l(la??(la=Pe()))),d.f|=Q)),N>$.size&&Lr(),k&&N>0&&_e(ea()),!b)if(y.set(m,$),C){for(const[ne,oe]of i)$.has(ne)||m.skip_effect(oe.e);m.oncommit(A),m.ondiscard(p)}else A(m);S&&le(!0),o(g)}),T={effect:w,items:i,pending:y,outrogroups:null,fallback:d};b=!1,k&&(n=ie)}function $e(e){for(;e!==null&&(e.f&Gr)===0;)e=e.next;return e}function Ts(e,a,t,r,s){var I,z,R,ne,oe,fe,xe,Te,he;var l=(r&Kr)!==0,n=a.length,i=e.items,c=$e(e.effect.first),_,d=null,g,h=[],y=[],b,A,p,w;if(l)for(w=0;w<n;w+=1)b=a[w],A=s(b,w),p=i.get(A).e,(p.f&Q)===0&&((z=(I=p.nodes)==null?void 0:I.a)==null||z.measure(),(g??(g=new Set)).add(p));for(w=0;w<n;w+=1){if(b=a[w],A=s(b,w),p=i.get(A).e,e.outrogroups!==null)for(const q of e.outrogroups)q.pending.delete(p),q.done.delete(p);if((p.f&ct)!==0&&(ba(p),l&&((ne=(R=p.nodes)==null?void 0:R.a)==null||ne.unfix(),(g??(g=new Set)).delete(p))),(p.f&Q)!==0)if(p.f^=Q,p===c)Se(p,null,t);else{var T=d?d.next:c;p===e.effect.last&&(e.effect.last=p.prev),p.prev&&(p.prev.next=p.next),p.next&&(p.next.prev=p.prev),re(e,d,p),re(e,p,T),Se(p,T,t),d=p,h=[],y=[],c=$e(d.next);continue}if(p!==c){if(_!==void 0&&_.has(p)){if(h.length<y.length){var N=y[0],S;d=N.prev;var V=h[0],$=h[h.length-1];for(S=0;S<h.length;S+=1)Se(h[S],N,t);for(S=0;S<y.length;S+=1)_.delete(y[S]);re(e,V.prev,$.next),re(e,d,V),re(e,$,N),c=N,d=$,w-=1,h=[],y=[]}else _.delete(p),Se(p,c,t),re(e,p.prev,p.next),re(e,p,d===null?e.effect.first:d.next),re(e,d,p),d=p;continue}for(h=[],y=[];c!==null&&c!==p;)(_??(_=new Set)).add(c),y.push(c),c=$e(c.next);if(c===null)continue}(p.f&Q)===0&&h.push(p),d=p,c=$e(p.next)}if(e.outrogroups!==null){for(const q of e.outrogroups)q.pending.size===0&&(xt(e,$t(q.done)),(oe=e.outrogroups)==null||oe.delete(q));e.outrogroups.size===0&&(e.outrogroups=null)}if(c!==null||_!==void 0){var m=[];if(_!==void 0)for(p of _)(p.f&ct)===0&&m.push(p);for(;c!==null;)(c.f&ct)===0&&c!==e.fallback&&m.push(c),c=$e(c.next);var C=m.length;if(C>0){var O=(r&$a)!==0&&n===0?t:null;if(l){for(w=0;w<C;w+=1)(xe=(fe=m[w].nodes)==null?void 0:fe.a)==null||xe.measure();for(w=0;w<C;w+=1)(he=(Te=m[w].nodes)==null?void 0:Te.a)==null||he.fix()}As(e,m,O)}}l&&ya(()=>{var q,ke;if(g!==void 0)for(p of g)(ke=(q=p.nodes)==null?void 0:q.a)==null||ke.apply()})}function ks(e,a,t,r,s,l,n,i){var c=(n&Dr)!==0?(n&Vr)===0?Wr(t,!1,!1):aa(t):null,_=(n&zr)!==0?aa(s):null;return{v:c,i:_,e:Ae(()=>(l(a,c??t,_??s,i),()=>{e.delete(r)}))}}function Se(e,a,t){if(e.nodes)for(var r=e.nodes.start,s=e.nodes.end,l=a&&(a.f&Q)===0?a.nodes.start:t;r!==null;){var n=qr(r);if(l.before(r),r===s)return;r=n}}function re(e,a,t){a===null?e.effect.first=t:a.next=t,t===null?e.effect.last=a:t.prev=a}function J(e,a,t,r,s){var i,c;if(k&&Re(),(i=a.$$host)!=null&&i.$$shadowRoot){const _=wa("slot");P(e,_);return}var l=(c=a.$$slots)==null?void 0:c[t],n=!1;l===!0&&(l=a.children,n=!0),l===void 0||l(e,n?()=>r:r)}function Cs(e,a,t,r,s,l){let n=k;k&&Re();var i=null;k&&ie.nodeType===Xr&&(i=ie,Re());var c=k?ie:e,_=new Es(c,!1);ha(()=>{const d=a()||null;var g=Qr;if(d===null){_.ensure(null,null);return}return _.ensure(d,h=>{if(d){if(i=k?i:wa(d,g),Cr(i,i),r){var y=null;k&&$s(d)&&i.append(y=document.createComment(""));var b=k?ma(i):i.appendChild(Pe());k&&(b===null?le(!1):_e(b)),r(i,b),y==null||y.remove()}Jr.nodes.end=i,h.before(i)}k&&_e(h)}),()=>{}},Zr),Sa(()=>{}),n&&(le(!0),_e(c))}function Ms(e,a){var t=void 0,r;Na(()=>{t!==(t=a())&&(r&&(Fe(r),r=null),t&&(r=Ae(()=>{Ea(()=>t(e))})))})}function Pa(e){var a,t,r="";if(typeof e=="string"||typeof e=="number")r+=e;else if(typeof e=="object")if(Array.isArray(e)){var s=e.length;for(a=0;a<s;a++)e[a]&&(t=Pa(e[a]))&&(r&&(r+=" "),r+=t)}else for(t in e)e[t]&&(r&&(r+=" "),r+=t);return r}function Is(){for(var e,a,t=0,r="",s=arguments.length;t<s;t++)(e=arguments[t])&&(a=Pa(e))&&(r&&(r+=" "),r+=a);return r}function Ps(e){return typeof e=="object"?Is(e):e??""}const oa=[...` 	
\r\f \v\uFEFF`];function Os(e,a,t){var r=e==null?"":""+e;if(t){for(var s of Object.keys(t))if(t[s])r=r?r+" "+s:s;else if(r.length)for(var l=s.length,n=0;(n=r.indexOf(s,n))>=0;){var i=n+l;(n===0||oa.includes(r[n-1]))&&(i===r.length||oa.includes(r[i]))?r=(n===0?"":r.substring(0,n))+r.substring(i+1):n=i}}return r===""?null:r}function fa(e,a=!1){var t=a?" !important;":";",r="";for(var s of Object.keys(e)){var l=e[s];l!=null&&l!==""&&(r+=" "+s+": "+l+t)}return r}function ut(e){return e[0]!=="-"||e[1]!=="-"?e.toLowerCase():e}function Rs(e,a){if(a){var t="",r,s;if(Array.isArray(a)?(r=a[0],s=a[1]):r=a,e){e=String(e).replaceAll(/\/\*.*?\*\//g,"").trim();var l=!1,n=0,i=!1,c=[];r&&c.push(...Object.keys(r).map(ut)),s&&c.push(...Object.keys(s).map(ut));var _=0,d=-1;const A=e.length;for(var g=0;g<A;g++){var h=e[g];if(i?h==="/"&&e[g-1]==="*"&&(i=!1):l?l===h&&(l=!1):h==="/"&&e[g+1]==="*"?i=!0:h==='"'||h==="'"?l=h:h==="("?n++:h===")"&&n--,!i&&l===!1&&n===0){if(h===":"&&d===-1)d=g;else if(h===";"||g===A-1){if(d!==-1){var y=ut(e.substring(_,d).trim());if(!c.includes(y)){h!==";"&&g++;var b=e.substring(_,g).trim();t+=" "+b+";"}}_=g+1,d=-1}}}}return r&&(t+=fa(r)),s&&(t+=fa(s,!0)),t=t.trim(),t===""?null:t}return e==null?null:String(e)}function Ne(e,a,t,r,s,l){var n=e[ra];if(k||n!==t||n===void 0){var i=Os(t,r,l);(!k||i!==e.getAttribute("class"))&&(i==null?e.removeAttribute("class"):a?e.className=i:e.setAttribute("class",i)),e[ra]=t}else if(l&&s!==l)for(var c in l){var _=!!l[c];(s==null||_!==!!s[c])&&e.classList.toggle(c,_)}return l}function vt(e,a={},t,r){for(var s in t){var l=t[s];a[s]!==l&&(t[s]==null?e.style.removeProperty(s):e.style.setProperty(s,l,r))}}function Oa(e,a,t,r){var s=e[sa];if(k||s!==a){var l=Rs(a,r);(!k||l!==e.getAttribute("style"))&&(l==null?e.removeAttribute("style"):e.style.cssText=l),e[sa]=a}else r&&(Array.isArray(r)?(vt(e,t==null?void 0:t[0],r[0]),vt(e,t==null?void 0:t[1],r[1],"important")):vt(e,t,r));return r}function Ra(e,a){a?e.hasAttribute("selected")||e.setAttribute("selected",""):e.removeAttribute("selected")}function da(e,a){var t=!("__defaultValue"in e);!t&&e.__defaultValue===a||(e.__defaultValue=a,Fa(e,!t||"__value"in e))}function Fa(e,a){var t=e.__defaultValue,r=e.multiple,s=r?t??[]:null;if(!(r&&!mt(s))){var l=e.selectedIndex,n=a&&r?new Set(e.selectedOptions):null;for(var i of e.options){var c=bt(i);Ra(i,r?s.includes(c):Aa(c,t))}if(a)if(n!==null)for(i of e.options){var _=n.has(i);i.selected!==_&&(i.selected=_)}else e.selectedIndex!==l&&(e.selectedIndex=l)}}function ht(e,a,t=!1){if(e.multiple){if(a==null)return;if(!mt(a))return es();for(var r of e.options)r.selected=a.includes(bt(r));return}for(r of e.options){var s=bt(r);if(Aa(s,a)){r.selected=!0;return}}(!t||a!==void 0)&&(e.selectedIndex=-1)}function Fs(e){var a=new MutationObserver(t=>{t.every(Ls)||("__defaultValue"in e&&Fa(e,!1),"__value"in e&&ht(e,e.__value))});a.observe(e,{childList:!0,subtree:!0,attributes:!0,attributeFilter:["value"]}),Sa(()=>{a.disconnect()})}function bt(e){return"__value"in e?e.__value:e.value}function Ls(e){if(e.target.closest("selectedcontent")!==null)return!0;if(e.type==="childList"){var a=[...e.addedNodes,...e.removedNodes];return a.length>0&&a.every(t=>t.nodeName==="SELECTEDCONTENT")}return!1}const ye=Symbol("class"),we=Symbol("style"),La=Symbol("is custom element"),ja=Symbol("is html"),js=je?"link":"LINK",ca=je?"input":"INPUT",Hs=je?"option":"OPTION",Ha=je?"select":"SELECT";function gt(e){if(k){var a=!1,t=()=>{if(!a){if(a=!0,e.hasAttribute("value")){var r=e.value;Ee(e,"value",null),e.value=r}if(e.hasAttribute("checked")){var s=e.checked;Ee(e,"checked",null),e.checked=s}}};e[ns]=t,ya(t),is()}}function Ee(e,a,t,r){var s=Da(e);k&&(s[a]=e.getAttribute(a),a==="src"||a==="srcset"||a==="href"&&e.nodeName===js)||s[a]!==(s[a]=t)&&(a==="loading"&&(e[ds]=t),t==null?e.removeAttribute(a):typeof t!="string"&&Va(e).has(a)?e[a]=t:e.setAttribute(a,t))}function Ds(e,a,t,r,s=!1,l=!1){k&&s&&e.nodeName===ca&&("defaultValue"in t||"defaultChecked"in t||gt(e));var n=Da(e),i=n[La],c=!n[ja];let _=k&&i;_&&le(!1);var d=a||{},g=e.nodeName===Hs,h=e.nodeName===Ha;for(var y in a)!(y in t)&&y[0]+y[1]!=="$$"&&(t[y]=null);t.class?t.class=Ps(t.class):t[ye]&&(t.class=null),t[we]&&(t.style??(t.style=null));var b=Va(e);if(e.nodeName===ca&&"type"in t&&("value"in t||"__value"in t)){var A=t.type;(A!==d.type||A===void 0&&e.hasAttribute("type"))&&(d.type=A,Ee(e,"type",A))}for(const $ in t){let m=t[$];if(g&&$==="value"&&m==null){e.value=e.__value="",d[$]=m;continue}if($==="class"){var p=e.namespaceURI==="http://www.w3.org/1999/xhtml";Ne(e,p,m,r,a==null?void 0:a[ye],t[ye]),d[$]=m,d[ye]=t[ye];continue}if($==="style"){Oa(e,m,a==null?void 0:a[we],t[we]),d[$]=m,d[we]=t[we];continue}var w=d[$];if(!(m===w&&!(m===void 0&&e.hasAttribute($)))){d[$]=m;var T=$[0]+$[1];if(T!=="$$")if(T==="on"){const C={},O="$$"+$;let I=$.slice(2);var N=Ns(I);if(ys(I)&&(I=I.slice(0,-7),C.capture=!0),!N&&w){if(m!=null)continue;e.removeEventListener(I,d[O],C),d[O]=null}if(N)se(I,e,m),Ca([I]);else if(m!=null){let z=function(R){d[$].call(this,R)};d[O]=ws(I,e,z,C)}}else if($==="style")Ee(e,$,m);else if($==="autofocus")rs(e,!!m);else if(!i&&($==="__value"||$==="value"&&m!=null))e.value=e.__value=m;else if($==="selected"&&g)Ra(e,m);else{var S=$;c||(S=Ss(S));var V=S==="defaultValue"||S==="defaultChecked";if(h&&S==="defaultValue")continue;if(m==null&&!i&&!V)if(n[$]=null,S==="value"||S==="checked"){let C=e;const O=a===void 0;if(S==="value"){let I=C.defaultValue;C.removeAttribute(S),C.defaultValue=I,C.value=C.__value=O?I:null}else{let I=C.defaultChecked;C.removeAttribute(S),C.defaultChecked=I,C.checked=O?I:!1}}else e.removeAttribute($);else V||(i||typeof m!="string")&&b.has(S)?(e[S]=m,S in n&&(n[S]=ss)):typeof m!="function"&&Ee(e,S,m)}}}return _&&le(!0),d}function ua(e,a,t=[],r=[],s=[],l,n=!1,i=!1){ts(s,t,r,c=>{var _=void 0,d={},g=e.nodeName===Ha,h=!1;if(Na(()=>{var b=a(...c.map(o)),A=Ds(e,_,b,l,n,i);if(h&&g){var p=e;"defaultValue"in b&&da(p,b.defaultValue),"value"in b&&ht(p,b.value)}for(let T of Object.getOwnPropertySymbols(d))b[T]||Fe(d[T]);for(let T of Object.getOwnPropertySymbols(b)){var w=b[T];T.description===as&&(!_||w!==_[T])&&(d[T]&&Fe(d[T]),d[T]=Ae(()=>Ms(e,()=>w))),A[T]=w}_=A}),g){var y=e;Ea(()=>{var b=_;"defaultValue"in b&&da(y,b.defaultValue),ht(y,b.value,!0),Fs(y)})}h=!0})}function Da(e){var a;return e[a=ls]??(e[a]={[La]:e.nodeName.includes("-"),[ja]:e.namespaceURI===os})}var va=new Map;function Va(e){var a=e.getAttribute("is")||e.nodeName,t=va.get(a);if(t)return t;va.set(a,t=new Set);for(var r,s=e,l=Element.prototype;l!==s;){r=cs(s);for(var n in r)r[n].set&&n!=="innerHTML"&&n!=="textContent"&&n!=="innerText"&&t.add(n);s=fs(s)}return t}function pa(e,a,t=a){var r=new WeakSet;us(e,"input",async s=>{var l=s?e.defaultValue:e.value;if(l=pt(e)?_t(l):l,t(l),ve!==null&&r.add(ve),await vs(),l!==(l=a())){var n=e.selectionStart,i=e.selectionEnd,c=e.value.length;if(e.value=l??"",i!==null){var _=e.value.length;n===i&&i===c&&_>c?(e.selectionStart=_,e.selectionEnd=_):(e.selectionStart=n,e.selectionEnd=Math.min(i,_))}}}),(k&&e.defaultValue!==e.value||Le(a)==null&&e.value)&&(t(pt(e)?_t(e.value):e.value),ve!==null&&r.add(ve)),ps(()=>{var s=a();if(e===document.activeElement){var l=ve;if(r.has(l))return}pt(e)&&s===_t(e.value)||e.type==="date"&&!s&&!e.value||s!==e.value&&(e.value=s??"")})}function pt(e){var a=e.type;return a==="number"||a==="range"}function _t(e){return e===""?null:+e}function Vs(e=!1){const a=_s,t=a.l.u;if(!t)return;let r=()=>pe(a.s);if(e){let s=0,l={};const n=bs(()=>{let i=!1;const c=a.s;for(const _ in c)c[_]!==l[_]&&(l[_]=c[_],i=!0);return i&&s++,s});r=()=>o(n)}t.b.length&&xs(()=>{_a(a,r),ia(t.b)}),na(()=>{const s=Le(()=>t.m.map(hs));return()=>{for(const l of s)typeof l=="function"&&l()}}),t.a.length&&na(()=>{_a(a,r),ia(t.a)})}function _a(e,a){if(e.l.s)for(const t of e.l.s)o(t);a()}gs();/**
 * @license lucide-svelte v0.474.0 - ISC
 *
 * ISC License
 * 
 * Copyright (c) for portions of Lucide are held by Cole Bemis 2013-2022 as part of Feather (MIT). All other copyright (c) for Lucide are held by Lucide Contributors 2022.
 * 
 * Permission to use, copy, modify, and/or distribute this software for any
 * purpose with or without fee is hereby granted, provided that the above
 * copyright notice and this permission notice appear in all copies.
 * 
 * THE SOFTWARE IS PROVIDED "AS IS" AND THE AUTHOR DISCLAIMS ALL WARRANTIES
 * WITH REGARD TO THIS SOFTWARE INCLUDING ALL IMPLIED WARRANTIES OF
 * MERCHANTABILITY AND FITNESS. IN NO EVENT SHALL THE AUTHOR BE LIABLE FOR
 * ANY SPECIAL, DIRECT, INDIRECT, OR CONSEQUENTIAL DAMAGES OR ANY DAMAGES
 * WHATSOEVER RESULTING FROM LOSS OF USE, DATA OR PROFITS, WHETHER IN AN
 * ACTION OF CONTRACT, NEGLIGENCE OR OTHER TORTIOUS ACTION, ARISING OUT OF
 * OR IN CONNECTION WITH THE USE OR PERFORMANCE OF THIS SOFTWARE.
 * 
 */const Ws={xmlns:"http://www.w3.org/2000/svg",width:24,height:24,viewBox:"0 0 24 24",fill:"none",stroke:"currentColor","stroke-width":2,"stroke-linecap":"round","stroke-linejoin":"round"};var zs=Mr("<svg><!><!></svg>");function te(e,a){const t=Y(a,["children","$$slots","$$events","$$legacy"]),r=Y(t,["name","color","size","strokeWidth","absoluteStrokeWidth","iconNode"]);Ta(a,!1);let s=ce(a,"name",8,void 0),l=ce(a,"color",8,"currentColor"),n=ce(a,"size",8,24),i=ce(a,"strokeWidth",8,2),c=ce(a,"absoluteStrokeWidth",8,!1),_=ce(a,"iconNode",24,()=>[]);const d=(...b)=>b.filter((A,p,w)=>!!A&&w.indexOf(A)===p).join(" ");Vs();var g=zs();ua(g,(b,A)=>({...Ws,...r,width:n(),height:n(),stroke:l(),"stroke-width":b,class:A}),[()=>(pe(c()),pe(i()),pe(n()),Le(()=>c()?Number(i())*24/Number(n()):i())),()=>(pe(s()),pe(t),Le(()=>d("lucide-icon","lucide",s()?`lucide-${s()}`:"",t.class)))]);var h=v(g);Ia(h,1,_,Ma,(b,A)=>{var p=Oe(()=>ms(o(A),2));let w=()=>o(p)[0],T=()=>o(p)[1];var N=X(),S=Z(N);Cs(S,w,!0,(V,$)=>{ua(V,()=>({...T()}))}),P(b,N)});var y=x(h);J(y,a,"default",{}),u(g),P(e,g),ka()}function Bs(e,a){const t=Y(a,["children","$$slots","$$events","$$legacy"]);/**
 * @license lucide-svelte v0.474.0 - ISC
 *
 * ISC License
 *
 * Copyright (c) for portions of Lucide are held by Cole Bemis 2013-2022 as part of Feather (MIT). All other copyright (c) for Lucide are held by Lucide Contributors 2022.
 *
 * Permission to use, copy, modify, and/or distribute this software for any
 * purpose with or without fee is hereby granted, provided that the above
 * copyright notice and this permission notice appear in all copies.
 *
 * THE SOFTWARE IS PROVIDED "AS IS" AND THE AUTHOR DISCLAIMS ALL WARRANTIES
 * WITH REGARD TO THIS SOFTWARE INCLUDING ALL IMPLIED WARRANTIES OF
 * MERCHANTABILITY AND FITNESS. IN NO EVENT SHALL THE AUTHOR BE LIABLE FOR
 * ANY SPECIAL, DIRECT, INDIRECT, OR CONSEQUENTIAL DAMAGES OR ANY DAMAGES
 * WHATSOEVER RESULTING FROM LOSS OF USE, DATA OR PROFITS, WHETHER IN AN
 * ACTION OF CONTRACT, NEGLIGENCE OR OTHER TORTIOUS ACTION, ARISING OUT OF
 * OR IN CONNECTION WITH THE USE OR PERFORMANCE OF THIS SOFTWARE.
 *
 */const r=[["path",{d:"M22 12h-2.48a2 2 0 0 0-1.93 1.46l-2.35 8.36a.25.25 0 0 1-.48 0L9.24 2.18a.25.25 0 0 0-.48 0l-2.35 8.36A2 2 0 0 1 4.49 12H2"}]];te(e,ee({name:"activity"},()=>t,{get iconNode(){return r},children:(s,l)=>{var n=X(),i=Z(n);J(i,a,"default",{}),P(s,n)},$$slots:{default:!0}}))}function Gs(e,a){const t=Y(a,["children","$$slots","$$events","$$legacy"]);/**
 * @license lucide-svelte v0.474.0 - ISC
 *
 * ISC License
 *
 * Copyright (c) for portions of Lucide are held by Cole Bemis 2013-2022 as part of Feather (MIT). All other copyright (c) for Lucide are held by Lucide Contributors 2022.
 *
 * Permission to use, copy, modify, and/or distribute this software for any
 * purpose with or without fee is hereby granted, provided that the above
 * copyright notice and this permission notice appear in all copies.
 *
 * THE SOFTWARE IS PROVIDED "AS IS" AND THE AUTHOR DISCLAIMS ALL WARRANTIES
 * WITH REGARD TO THIS SOFTWARE INCLUDING ALL IMPLIED WARRANTIES OF
 * MERCHANTABILITY AND FITNESS. IN NO EVENT SHALL THE AUTHOR BE LIABLE FOR
 * ANY SPECIAL, DIRECT, INDIRECT, OR CONSEQUENTIAL DAMAGES OR ANY DAMAGES
 * WHATSOEVER RESULTING FROM LOSS OF USE, DATA OR PROFITS, WHETHER IN AN
 * ACTION OF CONTRACT, NEGLIGENCE OR OTHER TORTIOUS ACTION, ARISING OUT OF
 * OR IN CONNECTION WITH THE USE OR PERFORMANCE OF THIS SOFTWARE.
 *
 */const r=[["rect",{width:"16",height:"10",x:"2",y:"7",rx:"2",ry:"2"}],["line",{x1:"22",x2:"22",y1:"11",y2:"13"}]];te(e,ee({name:"battery"},()=>t,{get iconNode(){return r},children:(s,l)=>{var n=X(),i=Z(n);J(i,a,"default",{}),P(s,n)},$$slots:{default:!0}}))}function xa(e,a){const t=Y(a,["children","$$slots","$$events","$$legacy"]);/**
 * @license lucide-svelte v0.474.0 - ISC
 *
 * ISC License
 *
 * Copyright (c) for portions of Lucide are held by Cole Bemis 2013-2022 as part of Feather (MIT). All other copyright (c) for Lucide are held by Lucide Contributors 2022.
 *
 * Permission to use, copy, modify, and/or distribute this software for any
 * purpose with or without fee is hereby granted, provided that the above
 * copyright notice and this permission notice appear in all copies.
 *
 * THE SOFTWARE IS PROVIDED "AS IS" AND THE AUTHOR DISCLAIMS ALL WARRANTIES
 * WITH REGARD TO THIS SOFTWARE INCLUDING ALL IMPLIED WARRANTIES OF
 * MERCHANTABILITY AND FITNESS. IN NO EVENT SHALL THE AUTHOR BE LIABLE FOR
 * ANY SPECIAL, DIRECT, INDIRECT, OR CONSEQUENTIAL DAMAGES OR ANY DAMAGES
 * WHATSOEVER RESULTING FROM LOSS OF USE, DATA OR PROFITS, WHETHER IN AN
 * ACTION OF CONTRACT, NEGLIGENCE OR OTHER TORTIOUS ACTION, ARISING OUT OF
 * OR IN CONNECTION WITH THE USE OR PERFORMANCE OF THIS SOFTWARE.
 *
 */const r=[["path",{d:"M7 16.3c2.2 0 4-1.83 4-4.05 0-1.16-.57-2.26-1.71-3.19S7.29 6.75 7 5.3c-.29 1.45-1.14 2.84-2.29 3.76S3 11.1 3 12.25c0 2.22 1.8 4.05 4 4.05z"}],["path",{d:"M12.56 6.6A10.97 10.97 0 0 0 14 3.02c.5 2.5 2 4.9 4 6.5s3 3.5 3 5.5a6.98 6.98 0 0 1-11.91 4.97"}]];te(e,ee({name:"droplets"},()=>t,{get iconNode(){return r},children:(s,l)=>{var n=X(),i=Z(n);J(i,a,"default",{}),P(s,n)},$$slots:{default:!0}}))}function Us(e,a){const t=Y(a,["children","$$slots","$$events","$$legacy"]);/**
 * @license lucide-svelte v0.474.0 - ISC
 *
 * ISC License
 *
 * Copyright (c) for portions of Lucide are held by Cole Bemis 2013-2022 as part of Feather (MIT). All other copyright (c) for Lucide are held by Lucide Contributors 2022.
 *
 * Permission to use, copy, modify, and/or distribute this software for any
 * purpose with or without fee is hereby granted, provided that the above
 * copyright notice and this permission notice appear in all copies.
 *
 * THE SOFTWARE IS PROVIDED "AS IS" AND THE AUTHOR DISCLAIMS ALL WARRANTIES
 * WITH REGARD TO THIS SOFTWARE INCLUDING ALL IMPLIED WARRANTIES OF
 * MERCHANTABILITY AND FITNESS. IN NO EVENT SHALL THE AUTHOR BE LIABLE FOR
 * ANY SPECIAL, DIRECT, INDIRECT, OR CONSEQUENTIAL DAMAGES OR ANY DAMAGES
 * WHATSOEVER RESULTING FROM LOSS OF USE, DATA OR PROFITS, WHETHER IN AN
 * ACTION OF CONTRACT, NEGLIGENCE OR OTHER TORTIOUS ACTION, ARISING OUT OF
 * OR IN CONNECTION WITH THE USE OR PERFORMANCE OF THIS SOFTWARE.
 *
 */const r=[["path",{d:"m12 14 4-4"}],["path",{d:"M3.34 19a10 10 0 1 1 17.32 0"}]];te(e,ee({name:"gauge"},()=>t,{get iconNode(){return r},children:(s,l)=>{var n=X(),i=Z(n);J(i,a,"default",{}),P(s,n)},$$slots:{default:!0}}))}function Ys(e,a){const t=Y(a,["children","$$slots","$$events","$$legacy"]);/**
 * @license lucide-svelte v0.474.0 - ISC
 *
 * ISC License
 *
 * Copyright (c) for portions of Lucide are held by Cole Bemis 2013-2022 as part of Feather (MIT). All other copyright (c) for Lucide are held by Lucide Contributors 2022.
 *
 * Permission to use, copy, modify, and/or distribute this software for any
 * purpose with or without fee is hereby granted, provided that the above
 * copyright notice and this permission notice appear in all copies.
 *
 * THE SOFTWARE IS PROVIDED "AS IS" AND THE AUTHOR DISCLAIMS ALL WARRANTIES
 * WITH REGARD TO THIS SOFTWARE INCLUDING ALL IMPLIED WARRANTIES OF
 * MERCHANTABILITY AND FITNESS. IN NO EVENT SHALL THE AUTHOR BE LIABLE FOR
 * ANY SPECIAL, DIRECT, INDIRECT, OR CONSEQUENTIAL DAMAGES OR ANY DAMAGES
 * WHATSOEVER RESULTING FROM LOSS OF USE, DATA OR PROFITS, WHETHER IN AN
 * ACTION OF CONTRACT, NEGLIGENCE OR OTHER TORTIOUS ACTION, ARISING OUT OF
 * OR IN CONNECTION WITH THE USE OR PERFORMANCE OF THIS SOFTWARE.
 *
 */const r=[["path",{d:"M12 2v10"}],["path",{d:"M18.4 6.6a9 9 0 1 1-12.77.04"}]];te(e,ee({name:"power"},()=>t,{get iconNode(){return r},children:(s,l)=>{var n=X(),i=Z(n);J(i,a,"default",{}),P(s,n)},$$slots:{default:!0}}))}function qs(e,a){const t=Y(a,["children","$$slots","$$events","$$legacy"]);/**
 * @license lucide-svelte v0.474.0 - ISC
 *
 * ISC License
 *
 * Copyright (c) for portions of Lucide are held by Cole Bemis 2013-2022 as part of Feather (MIT). All other copyright (c) for Lucide are held by Lucide Contributors 2022.
 *
 * Permission to use, copy, modify, and/or distribute this software for any
 * purpose with or without fee is hereby granted, provided that the above
 * copyright notice and this permission notice appear in all copies.
 *
 * THE SOFTWARE IS PROVIDED "AS IS" AND THE AUTHOR DISCLAIMS ALL WARRANTIES
 * WITH REGARD TO THIS SOFTWARE INCLUDING ALL IMPLIED WARRANTIES OF
 * MERCHANTABILITY AND FITNESS. IN NO EVENT SHALL THE AUTHOR BE LIABLE FOR
 * ANY SPECIAL, DIRECT, INDIRECT, OR CONSEQUENTIAL DAMAGES OR ANY DAMAGES
 * WHATSOEVER RESULTING FROM LOSS OF USE, DATA OR PROFITS, WHETHER IN AN
 * ACTION OF CONTRACT, NEGLIGENCE OR OTHER TORTIOUS ACTION, ARISING OUT OF
 * OR IN CONNECTION WITH THE USE OR PERFORMANCE OF THIS SOFTWARE.
 *
 */const r=[["path",{d:"M3 12a9 9 0 0 1 9-9 9.75 9.75 0 0 1 6.74 2.74L21 8"}],["path",{d:"M21 3v5h-5"}],["path",{d:"M21 12a9 9 0 0 1-9 9 9.75 9.75 0 0 1-6.74-2.74L3 16"}],["path",{d:"M8 16H3v5"}]];te(e,ee({name:"refresh-cw"},()=>t,{get iconNode(){return r},children:(s,l)=>{var n=X(),i=Z(n);J(i,a,"default",{}),P(s,n)},$$slots:{default:!0}}))}function Ks(e,a){const t=Y(a,["children","$$slots","$$events","$$legacy"]);/**
 * @license lucide-svelte v0.474.0 - ISC
 *
 * ISC License
 *
 * Copyright (c) for portions of Lucide are held by Cole Bemis 2013-2022 as part of Feather (MIT). All other copyright (c) for Lucide are held by Lucide Contributors 2022.
 *
 * Permission to use, copy, modify, and/or distribute this software for any
 * purpose with or without fee is hereby granted, provided that the above
 * copyright notice and this permission notice appear in all copies.
 *
 * THE SOFTWARE IS PROVIDED "AS IS" AND THE AUTHOR DISCLAIMS ALL WARRANTIES
 * WITH REGARD TO THIS SOFTWARE INCLUDING ALL IMPLIED WARRANTIES OF
 * MERCHANTABILITY AND FITNESS. IN NO EVENT SHALL THE AUTHOR BE LIABLE FOR
 * ANY SPECIAL, DIRECT, INDIRECT, OR CONSEQUENTIAL DAMAGES OR ANY DAMAGES
 * WHATSOEVER RESULTING FROM LOSS OF USE, DATA OR PROFITS, WHETHER IN AN
 * ACTION OF CONTRACT, NEGLIGENCE OR OTHER TORTIOUS ACTION, ARISING OUT OF
 * OR IN CONNECTION WITH THE USE OR PERFORMANCE OF THIS SOFTWARE.
 *
 */const r=[["circle",{cx:"11",cy:"11",r:"8"}],["path",{d:"m21 21-4.3-4.3"}]];te(e,ee({name:"search"},()=>t,{get iconNode(){return r},children:(s,l)=>{var n=X(),i=Z(n);J(i,a,"default",{}),P(s,n)},$$slots:{default:!0}}))}function Xs(e,a){const t=Y(a,["children","$$slots","$$events","$$legacy"]);/**
 * @license lucide-svelte v0.474.0 - ISC
 *
 * ISC License
 *
 * Copyright (c) for portions of Lucide are held by Cole Bemis 2013-2022 as part of Feather (MIT). All other copyright (c) for Lucide are held by Lucide Contributors 2022.
 *
 * Permission to use, copy, modify, and/or distribute this software for any
 * purpose with or without fee is hereby granted, provided that the above
 * copyright notice and this permission notice appear in all copies.
 *
 * THE SOFTWARE IS PROVIDED "AS IS" AND THE AUTHOR DISCLAIMS ALL WARRANTIES
 * WITH REGARD TO THIS SOFTWARE INCLUDING ALL IMPLIED WARRANTIES OF
 * MERCHANTABILITY AND FITNESS. IN NO EVENT SHALL THE AUTHOR BE LIABLE FOR
 * ANY SPECIAL, DIRECT, INDIRECT, OR CONSEQUENTIAL DAMAGES OR ANY DAMAGES
 * WHATSOEVER RESULTING FROM LOSS OF USE, DATA OR PROFITS, WHETHER IN AN
 * ACTION OF CONTRACT, NEGLIGENCE OR OTHER TORTIOUS ACTION, ARISING OUT OF
 * OR IN CONNECTION WITH THE USE OR PERFORMANCE OF THIS SOFTWARE.
 *
 */const r=[["path",{d:"M14 4v10.54a4 4 0 1 1-4 0V4a2 2 0 0 1 4 0Z"}]];te(e,ee({name:"thermometer"},()=>t,{get iconNode(){return r},children:(s,l)=>{var n=X(),i=Z(n);J(i,a,"default",{}),P(s,n)},$$slots:{default:!0}}))}function Zs(e,a){const t=Y(a,["children","$$slots","$$events","$$legacy"]);/**
 * @license lucide-svelte v0.474.0 - ISC
 *
 * ISC License
 *
 * Copyright (c) for portions of Lucide are held by Cole Bemis 2013-2022 as part of Feather (MIT). All other copyright (c) for Lucide are held by Lucide Contributors 2022.
 *
 * Permission to use, copy, modify, and/or distribute this software for any
 * purpose with or without fee is hereby granted, provided that the above
 * copyright notice and this permission notice appear in all copies.
 *
 * THE SOFTWARE IS PROVIDED "AS IS" AND THE AUTHOR DISCLAIMS ALL WARRANTIES
 * WITH REGARD TO THIS SOFTWARE INCLUDING ALL IMPLIED WARRANTIES OF
 * MERCHANTABILITY AND FITNESS. IN NO EVENT SHALL THE AUTHOR BE LIABLE FOR
 * ANY SPECIAL, DIRECT, INDIRECT, OR CONSEQUENTIAL DAMAGES OR ANY DAMAGES
 * WHATSOEVER RESULTING FROM LOSS OF USE, DATA OR PROFITS, WHETHER IN AN
 * ACTION OF CONTRACT, NEGLIGENCE OR OTHER TORTIOUS ACTION, ARISING OUT OF
 * OR IN CONNECTION WITH THE USE OR PERFORMANCE OF THIS SOFTWARE.
 *
 */const r=[["path",{d:"M12 20h.01"}],["path",{d:"M2 8.82a15 15 0 0 1 20 0"}],["path",{d:"M5 12.859a10 10 0 0 1 14 0"}],["path",{d:"M8.5 16.429a5 5 0 0 1 7 0"}]];te(e,ee({name:"wifi"},()=>t,{get iconNode(){return r},children:(s,l)=>{var n=X(),i=Z(n);J(i,a,"default",{}),P(s,n)},$$slots:{default:!0}}))}function Js(e,a){const t=Y(a,["children","$$slots","$$events","$$legacy"]);/**
 * @license lucide-svelte v0.474.0 - ISC
 *
 * ISC License
 *
 * Copyright (c) for portions of Lucide are held by Cole Bemis 2013-2022 as part of Feather (MIT). All other copyright (c) for Lucide are held by Lucide Contributors 2022.
 *
 * Permission to use, copy, modify, and/or distribute this software for any
 * purpose with or without fee is hereby granted, provided that the above
 * copyright notice and this permission notice appear in all copies.
 *
 * THE SOFTWARE IS PROVIDED "AS IS" AND THE AUTHOR DISCLAIMS ALL WARRANTIES
 * WITH REGARD TO THIS SOFTWARE INCLUDING ALL IMPLIED WARRANTIES OF
 * MERCHANTABILITY AND FITNESS. IN NO EVENT SHALL THE AUTHOR BE LIABLE FOR
 * ANY SPECIAL, DIRECT, INDIRECT, OR CONSEQUENTIAL DAMAGES OR ANY DAMAGES
 * WHATSOEVER RESULTING FROM LOSS OF USE, DATA OR PROFITS, WHETHER IN AN
 * ACTION OF CONTRACT, NEGLIGENCE OR OTHER TORTIOUS ACTION, ARISING OUT OF
 * OR IN CONNECTION WITH THE USE OR PERFORMANCE OF THIS SOFTWARE.
 *
 */const r=[["path",{d:"M12.8 19.6A2 2 0 1 0 14 16H2"}],["path",{d:"M17.5 8a2.5 2.5 0 1 1 2 4H2"}],["path",{d:"M9.8 4.4A2 2 0 1 1 11 8H2"}]];te(e,ee({name:"wind"},()=>t,{get iconNode(){return r},children:(s,l)=>{var n=X(),i=Z(n);J(i,a,"default",{}),P(s,n)},$$slots:{default:!0}}))}var Qs=ae('<div class="bg-red-950/40 border border-red-800/60 text-red-300 p-3.5 rounded-xl text-xs flex items-center justify-between"><span> </span> <button class="underline font-semibold ml-2">Retry</button></div>'),en=ae('<span class="px-2 py-0.5 rounded bg-cyan-500/10 text-cyan-400 text-xs font-bold font-mono"> </span>'),tn=ae('<span class="text-amber-400 ml-2">No I2C devices found</span>'),an=ae('<span class="px-2 py-0.5 rounded bg-cyan-950 border border-cyan-800 text-cyan-300"> </span>'),rn=ae('<div class="flex flex-wrap gap-1.5 mt-2"></div>'),sn=ae('<div class="p-3 rounded-xl bg-slate-950/80 border border-slate-800 text-xs font-mono"><span class="text-slate-400">I2C Detected:</span> <!></div>'),nn=ae('<p class="text-xs text-emerald-400 text-center">Settings saved to NVS! Connecting to WiFi...</p>'),ln=ae('<div class="space-y-3 pt-2"><p class="text-xs text-slate-400">Connect the ESP32 to your home router so you can access <a href="http://weather.local" class="text-cyan-400 font-mono underline">http://weather.local</a> from any PC or phone on your local network.</p> <div><label class="block text-[11px] text-slate-400 mb-1">WiFi Network Name (SSID)</label> <input type="text" placeholder="MyHomeWiFi" class="w-full px-3 py-2 rounded-xl bg-slate-950 border border-slate-800 text-slate-200 text-xs focus:outline-none focus:border-cyan-500"/></div> <div><label class="block text-[11px] text-slate-400 mb-1">WiFi Password</label> <input type="password" placeholder="Password" class="w-full px-3 py-2 rounded-xl bg-slate-950 border border-slate-800 text-slate-200 text-xs focus:outline-none focus:border-cyan-500"/></div> <button class="w-full py-2.5 rounded-xl bg-cyan-500 hover:bg-cyan-400 text-slate-950 font-bold text-xs transition-colors">Save & Connect</button> <!></div>'),on=ae('<div class="max-w-2xl mx-auto p-4 sm:p-6 space-y-4"><header class="bg-slate-900/90 border border-slate-800 rounded-2xl p-4 shadow-xl backdrop-blur-md"><div class="flex items-center justify-between"><div class="flex items-center gap-3"><div class="relative flex items-center justify-center w-10 h-10 rounded-xl bg-cyan-500/10 border border-cyan-500/20 text-cyan-400 font-bold"><!></div> <div><div class="flex items-center gap-2"><h1 class="font-bold text-lg text-slate-100"> </h1> <span><span></span> </span></div> <p class="text-xs text-slate-400">mDNS: <a href="http://weather.local" class="text-cyan-400 underline font-mono">http://weather.local</a> <span class="mx-1 text-slate-600">·</span> IP: <span class="font-mono text-slate-300"> </span></p></div></div> <div class="flex items-center gap-2"><button class="p-2 rounded-xl bg-slate-800 hover:bg-slate-700 text-slate-300 transition-colors" title="Manual Refresh"><!></button></div></div></header> <!> <section class="bg-slate-900/60 border border-slate-800/80 rounded-2xl p-4 space-y-3"><div class="flex items-center justify-between"><div class="flex items-center gap-2 text-slate-300 font-semibold text-sm"><!> <span>12V Battery Power Rail</span></div> <span class="text-xs font-mono px-2 py-0.5 rounded bg-slate-800 text-slate-300"> </span></div> <div class="flex items-end justify-between"><div><div class="text-2xl font-black text-slate-100 font-mono tracking-tight"> <span class="text-sm font-normal text-slate-400">V</span></div> <p class="text-xs text-slate-400">4S LiFePO4 · <span class="font-mono"> </span> V/cell</p></div> <div class="text-right"><span> </span></div></div> <div class="w-full bg-slate-800 h-2 rounded-full overflow-hidden"><div class="h-full bg-emerald-500 transition-all duration-500"></div></div></section> <div class="grid grid-cols-2 gap-3"><div class="bg-slate-900/60 border border-slate-800/80 rounded-2xl p-4 flex flex-col justify-between"><div class="flex items-center justify-between text-slate-400 text-xs"><span>Temperature</span> <!></div> <div class="my-2"><div class="text-2xl font-black text-slate-100 font-mono"> <span class="text-sm font-normal text-slate-400">°C</span></div> <div class="text-xs text-slate-400 flex items-center justify-between mt-1"><span>DS18B20 Probe:</span> <span class="font-mono text-cyan-400"> </span></div></div> <span class="text-[10px] text-slate-500">BME280 / BMP280</span></div> <div class="bg-slate-900/60 border border-slate-800/80 rounded-2xl p-4 flex flex-col justify-between"><div class="flex items-center justify-between text-slate-400 text-xs"><span>Humidity</span> <!></div> <div class="my-2"><div class="text-2xl font-black text-slate-100 font-mono"> <span class="text-sm font-normal text-slate-400">%</span></div> <p class="text-xs text-slate-400 mt-1">Relative Humidity</p></div> <span class="text-[10px] text-slate-500">BME280 Sensor</span></div> <div class="bg-slate-900/60 border border-slate-800/80 rounded-2xl p-4 flex flex-col justify-between"><div class="flex items-center justify-between text-slate-400 text-xs"><span>Pressure</span> <!></div> <div class="my-2"><div class="text-2xl font-black text-slate-100 font-mono"> <span class="text-sm font-normal text-slate-400">hPa</span></div> <p class="text-xs text-slate-400 mt-1">Barometric</p></div> <span class="text-[10px] text-slate-500">I2C Bus</span></div> <div class="bg-slate-900/60 border border-slate-800/80 rounded-2xl p-4 flex flex-col justify-between"><div class="flex items-center justify-between text-slate-400 text-xs"><span>Soil Moisture</span> <!></div> <div class="my-2"><div class="text-2xl font-black text-slate-100 font-mono"> <span class="text-sm font-normal text-slate-400">%</span></div> <p class="text-xs text-slate-400 font-mono mt-1"> </p></div> <span class="text-[10px] text-slate-500">GPIO13 Analog</span></div></div> <section class="bg-slate-900/60 border border-slate-800/80 rounded-2xl p-4 space-y-3"><div class="flex items-center justify-between text-xs text-slate-400"><div class="flex items-center gap-1.5 font-semibold text-slate-300 text-sm"><!> <span>RS485 Modbus Wind Station</span></div> <span class="text-[10px] font-mono bg-slate-800 px-2 py-0.5 rounded text-slate-400">UART1 @ 9600 Baud</span></div> <div class="grid grid-cols-2 gap-4"><div><span class="text-xs text-slate-400">Wind Speed (ID 1)</span> <div class="text-2xl font-black text-slate-100 font-mono mt-0.5"> <span class="text-sm font-normal text-slate-400">m/s</span></div></div> <div><span class="text-xs text-slate-400">Wind Direction (ID 2)</span> <div class="flex items-center gap-2 mt-0.5"><div class="text-2xl font-black text-slate-100 font-mono"> </div> <!></div></div></div></section> <section class="bg-slate-900/60 border border-slate-800/80 rounded-2xl p-4 flex items-center justify-between"><div><div class="text-xs text-slate-400">Rain Gauge (Reed Switch Interrupt)</div> <div class="text-2xl font-black text-slate-100 font-mono mt-1"> <span class="text-sm font-normal text-slate-400">mm</span> <span class="text-xs text-slate-400 font-normal ml-1"> </span></div></div> <button class="px-3 py-1.5 rounded-xl bg-slate-800 hover:bg-slate-700 text-xs font-medium text-slate-300 border border-slate-700 transition-colors"> </button></section> <section class="bg-slate-900/60 border border-slate-800/80 rounded-2xl p-4 space-y-3"><h2 class="text-xs font-semibold text-slate-400 uppercase tracking-wider">Hardware Testing & Controls</h2> <div class="grid grid-cols-2 gap-3"><button><!> <span> </span></button> <button class="flex items-center justify-center gap-2 p-3 rounded-xl bg-slate-800 hover:bg-slate-700 border border-slate-700 text-slate-300 font-medium text-xs transition-colors"><!> <span> </span></button></div> <!></section> <section class="bg-slate-900/60 border border-slate-800/80 rounded-2xl p-4 space-y-3"><button class="w-full flex items-center justify-between text-xs font-semibold text-slate-400 uppercase tracking-wider"><div class="flex items-center gap-1.5"><!> <span>Connect to Home/Office WiFi (STA Mode)</span></div> <span class="text-cyan-400 font-mono text-[10px]"> </span></button> <!></section> <footer class="text-center text-[11px] text-slate-500 py-2">ESP32-S3 N16R8 · Weather Station Research Node · Firmware v1.1.0-e22</footer></div>');function _n(e,a){Ta(a,!0);let t=K(null),r=K(!0),s=K(null),l=K(!1),n=K(!1),i=K(null),c=K(!1),_=K(!1),d=K(""),g=K(""),h=K(!1);async function y(){try{const f=await fetch("/api/telemetry");if(!f.ok)throw new Error(`HTTP ${f.status}`);H(t,await f.json(),!0),H(s,null)}catch(f){H(s,f.message||"Connection lost",!0)}finally{H(r,!1)}}async function b(){H(l,!0);try{const f=await fetch("/api/mosfet",{method:"POST"});if(f.ok){const E=await f.json();o(t)&&(o(t).mosfet_on=E.mosfet_on)}}catch(f){console.error(f)}finally{H(l,!1)}}async function A(){H(n,!0),H(i,null);try{const f=await fetch("/api/scan-i2c");if(f.ok){const E=await f.json();H(i,E.devices||[],!0)}}catch(f){console.error(f)}finally{H(n,!1)}}async function p(){H(c,!0);try{(await fetch("/api/rain/reset",{method:"POST"})).ok&&o(t)&&(o(t).rain_tips=0,o(t).rain_mm=0)}catch(f){console.error(f)}finally{H(c,!1)}}async function w(){if(o(d))try{(await fetch("/api/wifi",{method:"POST",headers:{"Content-Type":"application/json"},body:JSON.stringify({ssid:o(d),password:o(g)})})).ok&&(H(h,!0),setTimeout(()=>H(h,!1),4e3))}catch(f){console.error(f)}}function T(f){return f>=337.5||f<22.5?"N":f>=22.5&&f<67.5?"NE":f>=67.5&&f<112.5?"E":f>=112.5&&f<157.5?"SE":f>=157.5&&f<202.5?"S":f>=202.5&&f<247.5?"SW":f>=247.5&&f<292.5?"W":"NW"}const N=[[10,0],[12,5],[12.4,10],[12.8,20],[12.88,30],[13,40],[13.04,50],[13.08,60],[13.2,70],[13.28,80],[13.4,90],[13.6,99],[13.8,100]];function S(f){if(!Number.isFinite(f)||f<=N[0][0])return 0;const E=N[N.length-1];if(f>=E[0])return 100;for(let L=1;L<N.length;L++){const[W,B]=N[L-1],[D,G]=N[L];if(f<=D)return Math.round(B+(f-W)/(D-W)*(G-B))}return 100}Ir(()=>{y();const f=setInterval(()=>{y()},1500);return()=>clearInterval(f)});var V=on(),$=v(V),m=v($),C=v(m),O=v(C),I=v(O);Bs(I,{class:"w-5 h-5 animate-pulse"}),u(O);var z=x(O,2),R=v(z),ne=v(R),oe=j(ne),fe=x(ne,2),xe=v(fe),Te=x(xe);u(fe),u(R);var he=x(R,2),q=x(v(he),5),ke=j(q,!0);u(he),u(z),u(C);var yt=x(C,2),He=v(yt),Wa=v(He);{let f=Oe(()=>o(r)?"animate-spin":"");qs(Wa,{get class(){return`w-4 h-4 ${o(f)??""}`}})}u(He),u(yt),u(m),u($);var wt=x($,2);{var za=f=>{var E=Qs(),L=v(E),W=j(L),B=x(L,2);u(E),Ie(()=>M(W,`${o(s)??""} — ESP32 not responding or disconnected from WiFi`)),se("click",B,y),P(f,E)};ue(wt,f=>{o(s)&&f(za)})}var De=x(wt,2),Ve=v(De),We=v(Ve),Ba=v(We);Gs(Ba,{class:"w-4 h-4 text-emerald-400"}),F(2),u(We);var Ga=x(We,2),Ua=j(Ga);u(Ve);var ze=x(Ve,2),Be=v(ze),Ge=v(Be),Ya=v(Ge);F(),u(Ge);var St=x(Ge,2),qa=x(v(St)),Ka=j(qa,!0);F(),u(St),u(Be);var Nt=x(Be,2),Et=v(Nt),Xa=j(Et);u(Nt),u(ze);var Za=x(ze,2),Ja=j(Za);u(De);var Ue=x(De,2),Ye=v(Ue),qe=v(Ye),Qa=x(v(qe),2);Xs(Qa,{class:"w-4 h-4 text-orange-400"}),u(qe);var At=x(qe,2),Ke=v(At),er=v(Ke);F(),u(Ke);var Tt=x(Ke,2),tr=x(v(Tt),2),ar=j(tr,!0);u(Tt),u(At),F(2),u(Ye);var Xe=x(Ye,2),Ze=v(Xe),rr=x(v(Ze),2);xa(rr,{class:"w-4 h-4 text-blue-400"}),u(Ze);var kt=x(Ze,2),Ct=v(kt),sr=v(Ct);F(),u(Ct),F(2),u(kt),F(2),u(Xe);var Je=x(Xe,2),Qe=v(Je),nr=x(v(Qe),2);Us(nr,{class:"w-4 h-4 text-indigo-400"}),u(Qe);var Mt=x(Qe,2),It=v(Mt),ir=v(It);F(),u(It),F(2),u(Mt),F(2),u(Je);var Pt=x(Je,2),et=v(Pt),lr=x(v(et),2);xa(lr,{class:"w-4 h-4 text-emerald-400"}),u(et);var Ot=x(et,2),tt=v(Ot),or=v(tt);F(),u(tt);var fr=x(tt,2),dr=j(fr);u(Ot),F(2),u(Pt),u(Ue);var at=x(Ue,2),rt=v(at),Rt=v(rt),cr=v(Rt);Js(cr,{class:"w-4 h-4 text-cyan-400"}),F(2),u(Rt),F(2),u(rt);var Ft=x(rt,2),st=v(Ft),Lt=x(v(st),2),ur=v(Lt);F(),u(Lt),u(st);var jt=x(st,2),Ht=x(v(jt),2),Dt=v(Ht),vr=j(Dt,!0),pr=x(Dt,2);{var _r=f=>{var E=en(),L=j(E,!0);Ie(W=>M(L,W),[()=>T(o(t).wind_dir)]),P(f,E)};ue(pr,f=>{o(t)&&o(t).wind_dir<=360&&f(_r)})}u(Ht),u(jt),u(Ft),u(at);var nt=x(at,2),it=v(nt),Vt=x(v(it),2),Wt=v(Vt),xr=x(Wt,3),hr=j(xr);u(Vt),u(it);var lt=x(it,2),br=j(lt,!0);u(nt);var ot=x(nt,2),ft=x(v(ot),2),de=v(ft),zt=v(de);{let f=Oe(()=>{var E;return(E=o(t))!=null&&E.mosfet_on?"text-cyan-400":"text-slate-500"});Ys(zt,{get class(){return`w-4 h-4 ${o(f)??""}`}})}var gr=x(zt,2),mr=j(gr);u(de);var Ce=x(de,2),Bt=v(Ce);{let f=Oe(()=>o(n)?"animate-spin":"");Ks(Bt,{get class(){return`w-4 h-4 text-cyan-400 ${o(f)??""}`}})}var $r=x(Bt,2),yr=j($r,!0);u(Ce),u(ft);var wr=x(ft,2);{var Sr=f=>{var E=sn(),L=x(v(E),2);{var W=D=>{var G=tn();P(D,G)},B=D=>{var G=rn();Ia(G,21,()=>o(i),Ma,(be,ge)=>{var U=an(),me=j(U,!0);Ie(()=>M(me,o(ge))),P(be,U)}),u(G),P(D,G)};ue(L,D=>{o(i).length===0?D(W):D(B,-1)})}u(E),P(f,E)};ue(wr,f=>{o(i)&&f(Sr)})}u(ot);var Gt=x(ot,2),Me=v(Gt),dt=v(Me),Nr=v(dt);Zs(Nr,{class:"w-4 h-4 text-cyan-400"}),F(2),u(dt);var Er=x(dt,2),Ar=j(Er,!0);u(Me);var Tr=x(Me,2);{var kr=f=>{var E=ln(),L=x(v(E),2),W=x(v(L),2);gt(W),u(L);var B=x(L,2),D=x(v(B),2);gt(D),u(B);var G=x(B,2),be=x(G,2);{var ge=U=>{var me=nn();P(U,me)};ue(be,U=>{o(h)&&U(ge)})}u(E),pa(W,()=>o(d),U=>H(d,U)),pa(D,()=>o(g),U=>H(g,U)),se("click",G,w),P(f,E)};ue(Tr,f=>{o(_)&&f(kr)})}u(Gt),F(2),u(V),Ie((f,E,L,W,B,D,G,be,ge,U,me)=>{var Ut,Yt,qt,Kt,Xt,Zt,Jt,Qt;M(oe,`Weather Node #${((Ut=o(t))==null?void 0:Ut.node_id)??1??""}`),Ne(fe,1,`inline-flex items-center gap-1 px-2 py-0.5 rounded-full text-xs font-medium ${o(s)?"bg-red-500/10 text-red-400 border border-red-500/20":"bg-emerald-500/10 text-emerald-400 border border-emerald-500/20"}`),Ne(xe,1,`w-1.5 h-1.5 rounded-full ${o(s)?"bg-red-500":"bg-emerald-500"}`),M(Te,` ${o(s)?"Offline":"Live"}`),M(ke,((Yt=o(t))==null?void 0:Yt.sta_ip)||((qt=o(t))==null?void 0:qt.ap_ip)||"192.168.4.1"),M(Ua,`ADC: ${((Kt=o(t))==null?void 0:Kt.battery_raw_mv)??"—"??""} mV`),M(Ya,`${f??""} `),M(Ka,E),Ne(Et,1,`text-sm font-bold font-mono ${L??""}`),M(Xa,`${W??""}%`),Oa(Ja,`width: ${B??""}%`),M(er,`${D??""} `),M(ar,G),M(sr,`${be??""} `),M(ir,`${ge??""} `),M(or,`${(o(t)?o(t).soil_moist:"—")??""} `),M(dr,`ADC: ${((Xt=o(t))==null?void 0:Xt.soil_raw_mv)??"—"??""} mV`),M(ur,`${U??""} `),M(vr,o(t)&&o(t).wind_dir<=360?`${o(t).wind_dir}°`:"Timeout"),M(Wt,`${me??""} `),M(hr,`(${((Zt=o(t))==null?void 0:Zt.rain_tips)??0??""} tips)`),lt.disabled=o(c),M(br,o(c)?"Resetting...":"Reset Rain"),de.disabled=o(l),Ne(de,1,`flex items-center justify-center gap-2 p-3 rounded-xl border font-medium text-xs transition-colors ${(Jt=o(t))!=null&&Jt.mosfet_on?"bg-cyan-500/10 border-cyan-500/30 text-cyan-400 hover:bg-cyan-500/20":"bg-slate-800/60 border-slate-700 text-slate-400 hover:bg-slate-800"}`),M(mr,`12V_SW MOSFET: ${(Qt=o(t))!=null&&Qt.mosfet_on?"ON":"OFF"}`),Ce.disabled=o(n),M(yr,o(n)?"Scanning...":"Scan I2C Bus"),M(Ar,o(_)?"▲ Hide":"▼ Setup")},[()=>o(t)?o(t).battery_v.toFixed(2):"—",()=>o(t)?(o(t).battery_v/4).toFixed(2):"—",()=>o(t)&&S(o(t).battery_v)>20?"text-emerald-400":"text-amber-400",()=>o(t)?S(o(t).battery_v):0,()=>o(t)?S(o(t).battery_v):0,()=>o(t)?o(t).bme_temp.toFixed(1):"—",()=>o(t)&&o(t).ds18b20_temp>-100?`${o(t).ds18b20_temp.toFixed(1)}°C`:"N/A",()=>o(t)?o(t).bme_hum.toFixed(1):"—",()=>o(t)?o(t).bme_press.toFixed(1):"—",()=>o(t)&&o(t).wind_speed>=0?o(t).wind_speed.toFixed(1):"Timeout",()=>{var f,E;return((E=(f=o(t))==null?void 0:f.rain_mm)==null?void 0:E.toFixed(2))??"0.00"}]),se("click",He,()=>y()),se("click",lt,p),se("click",de,b),se("click",Ce,A),se("click",Me,()=>H(_,!o(_))),P(e,V),ka()}Ca(["click"]);export{_n as component};
